KevinQuigs/ECE1896-Force-Feedback-Telepresence-Robot/3D_Printing_Files/Robot/Inmoov Chest - 2175499/files/2pc_Chest__Back__A.stl

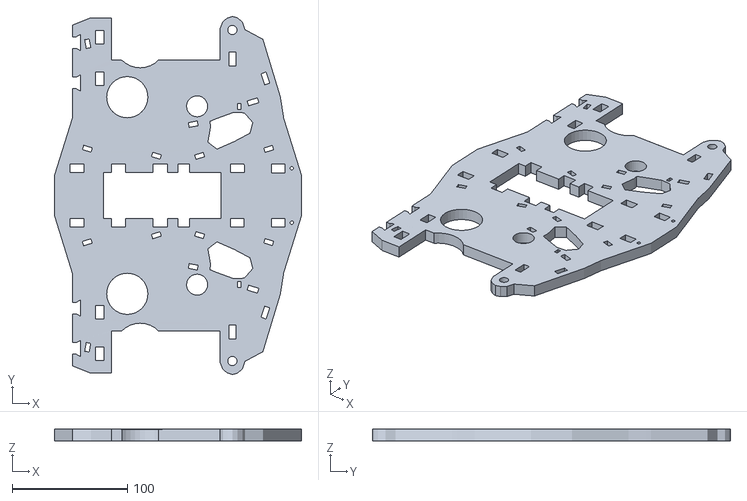
[picture p30: CAD file, 2025-10-10]
3D_Printing_Files/Robot/Inmoov Chest - 2175499/files/2pc_Chest__Back__A.stl
214.0 x 310.3 x 10.0
