KevinQuigs/ECE1896-Force-Feedback-Telepresence-Robot/3D_Printing_Files/Robot/Inmoov-hand-i2/Inmoov-hand-i2/i2_LeftHand/i2_LeftCoverThumbV3.stl

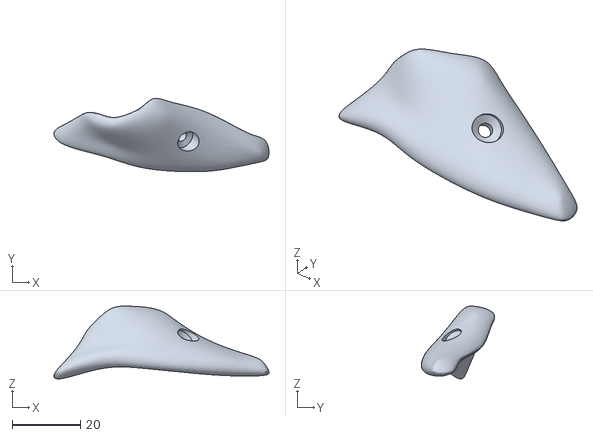
[picture p31: CAD file, 2025-10-01]
3D_Printing_Files/Robot/Inmoov-hand-i2/Inmoov-hand-i2/i2_LeftHand/i2_LeftCoverThumbV3.stl
63.1 x 21.6 x 21.4
