KevinQuigs/ECE1896-Force-Feedback-Telepresence-Robot/3D_Printing_Files/Robot/RoboticHead_Release1/STL/Head_base_mount.stl

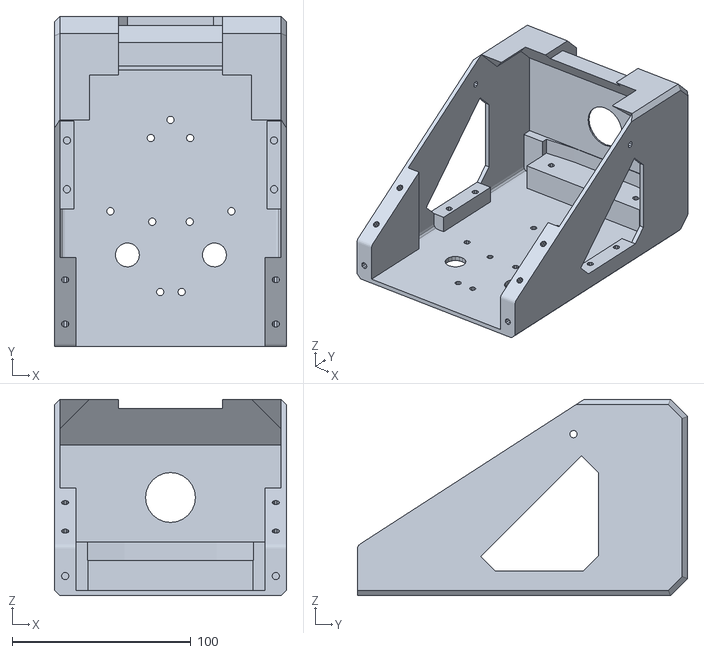
[picture p32: CAD file, 2025-10-10]
3D_Printing_Files/Robot/RoboticHead_Release1/STL/Head_base_mount.stl
130.0 x 184.9 x 110.0
