KevinQuigs/ECE1896-Force-Feedback-Telepresence-Robot/3D_Printing_Files/Robot/RoboticNeck_Release1/STL/Gear_Cover.stl

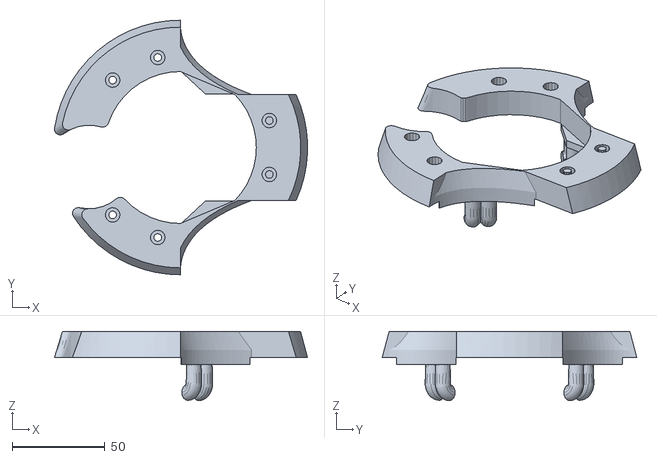
[picture p33: CAD file, 2025-10-10]
3D_Printing_Files/Robot/RoboticNeck_Release1/STL/Gear_Cover.stl
136.3 x 137.2 x 37.4
