KevinQuigs/ECE1896-Force-Feedback-Telepresence-Robot/3D_Printing_Files/Robot/Shoulder for Robot InMoov - 40040/files/servoholderV1.stl

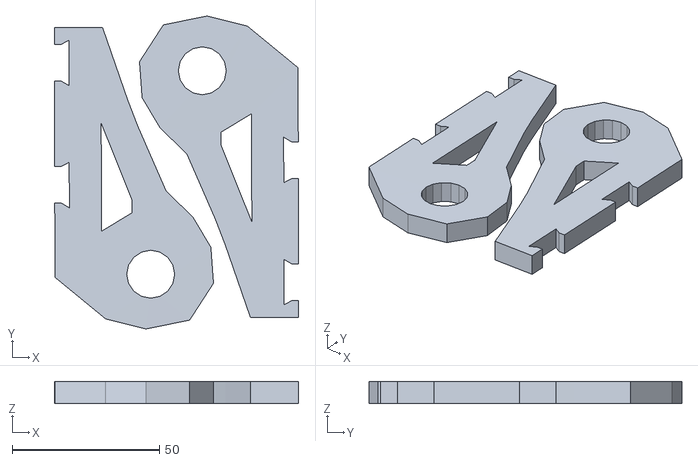
[picture p34: CAD file, 2025-10-01]
3D_Printing_Files/Robot/Shoulder for Robot InMoov - 40040/files/servoholderV1.stl
82.8 x 106.2 x 7.56
