KevinQuigs/ECE1896-Force-Feedback-Telepresence-Robot/3D_Printing_Files/Force_Feedback_Glove/LucidVrGloves/Prot4_EndCap.STL

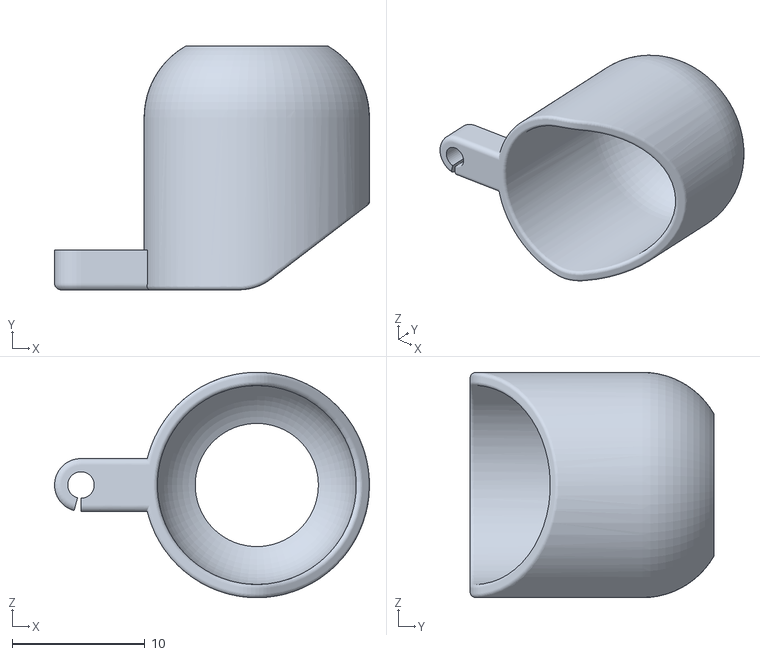
[picture p35: CAD file, 2025-10-01]
3D_Printing_Files/Force_Feedback_Glove/LucidVrGloves/Prot4_EndCap.STL
23.8 x 18.4 x 17.0
