KevinQuigs/ECE1896-Force-Feedback-Telepresence-Robot/3D_Printing_Files/Robot/Inmoov Chest - 2175499/files/4pc_Chest_Front_BottomLeft.stl

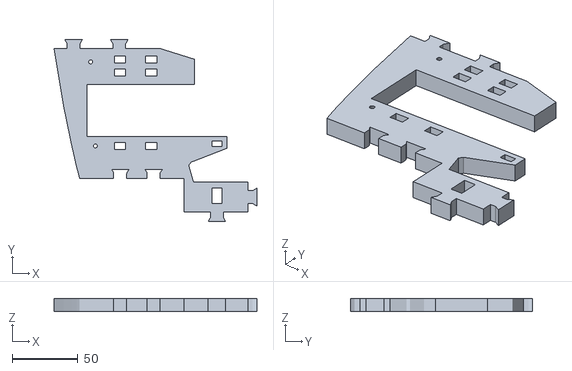
[picture p36: CAD file, 2025-10-10]
3D_Printing_Files/Robot/Inmoov Chest - 2175499/files/4pc_Chest_Front_BottomLeft.stl
154.4 x 138.7 x 10.0
