KevinQuigs/ECE1896-Force-Feedback-Telepresence-Robot/3D_Printing_Files/Robot/Inmoov-hand-i2/Inmoov-hand-i2/i2_RightHand/i2_HandCoverV2.stl

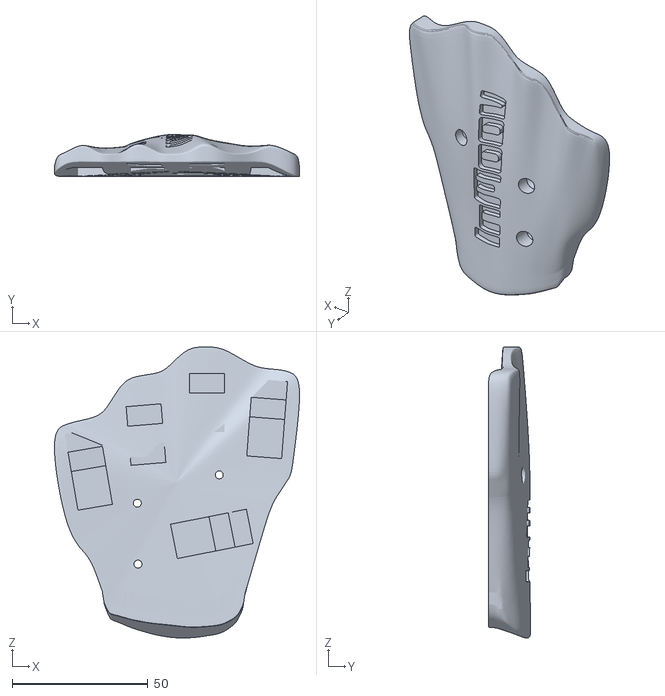
[picture p37: CAD file, 2025-10-01]
3D_Printing_Files/Robot/Inmoov-hand-i2/Inmoov-hand-i2/i2_RightHand/i2_HandCoverV2.stl
90.2 x 15.6 x 107.1
