KevinQuigs/ECE1896-Force-Feedback-Telepresence-Robot/3D_Printing_Files/Robot/RoboticHead_Release1/STL/Head_Handle.stl

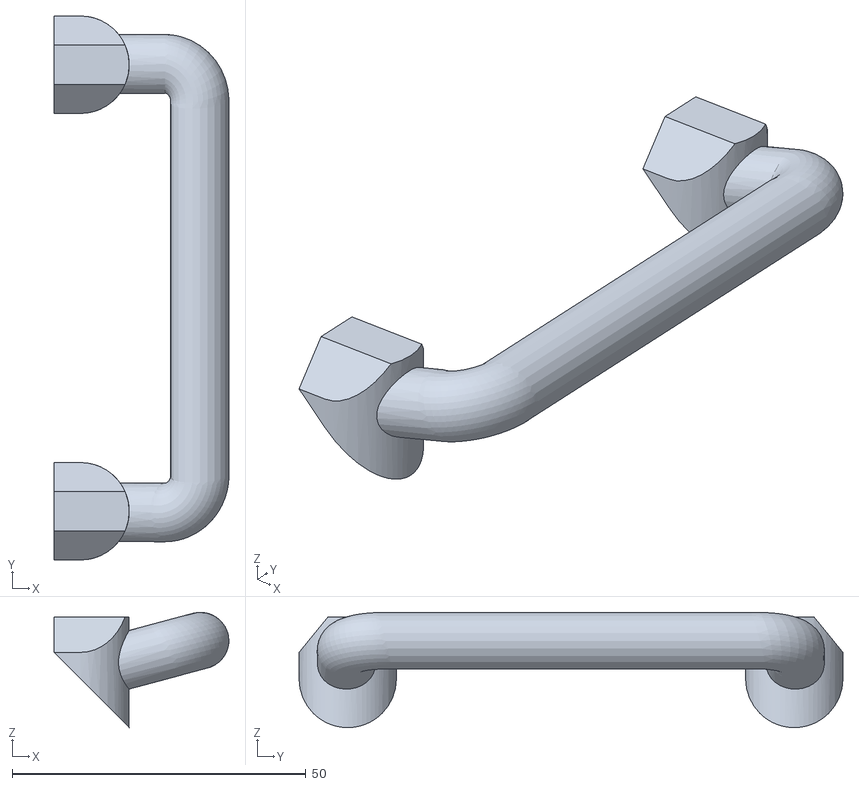
[picture p38: CAD file, 2025-10-10]
3D_Printing_Files/Robot/RoboticHead_Release1/STL/Head_Handle.stl
29.8 x 92.6 x 19.6
