KevinQuigs/ECE1896-Force-Feedback-Telepresence-Robot/3D_Printing_Files/Robot/RoboticNeck_Release1/STL/Test_BearingFilling.stl

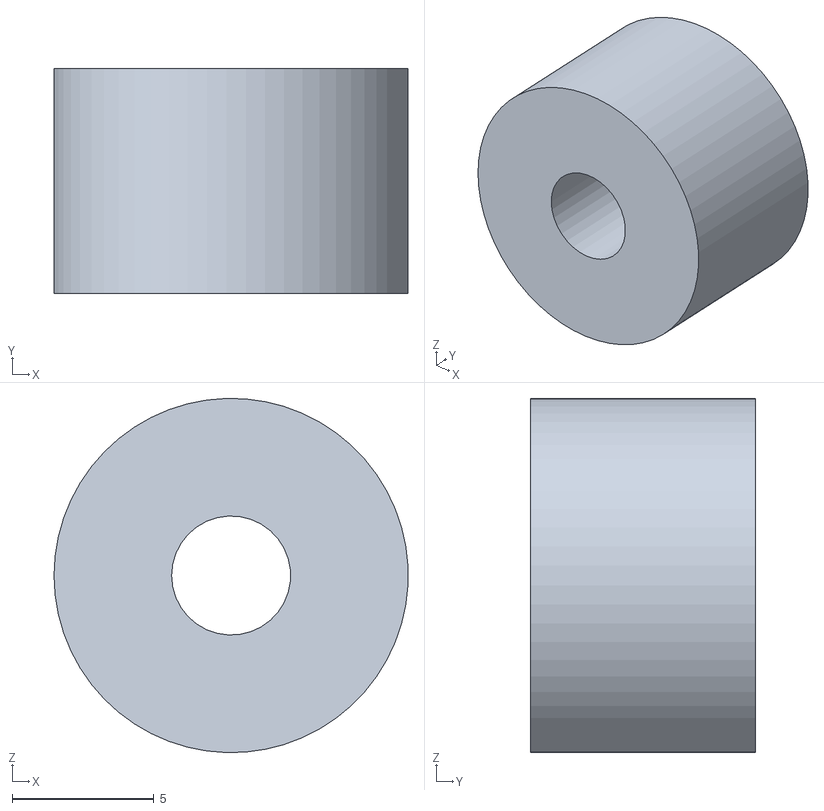
[picture p39: CAD file, 2025-10-10]
3D_Printing_Files/Robot/RoboticNeck_Release1/STL/Test_BearingFilling.stl
12.5 x 7.94 x 12.5
