KevinQuigs/ECE1896-Force-Feedback-Telepresence-Robot/3D_Printing_Files/Robot/Shoulder for Robot InMoov - 40040/files/servoHolsterV1.stl

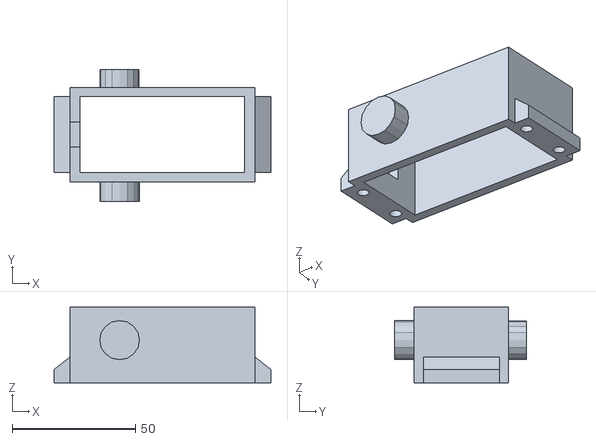
[picture p40: CAD file, 2025-10-01]
3D_Printing_Files/Robot/Shoulder for Robot InMoov - 40040/files/servoHolsterV1.stl
87.9 x 53.5 x 30.7
