KevinQuigs/ECE1896-Force-Feedback-Telepresence-Robot/3D_Printing_Files/Force_Feedback_Glove/LucidVrGloves/GreenPotSildeHolder_Proto4.1.STL

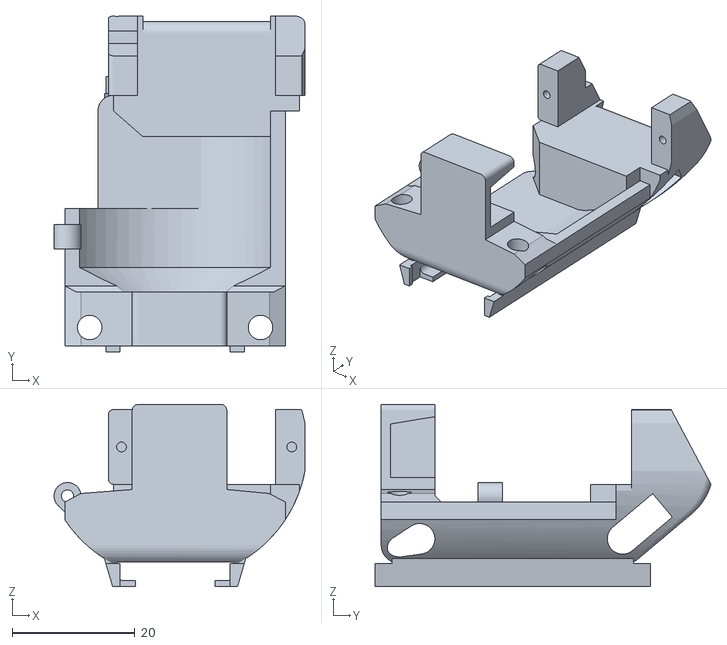
[picture p41: CAD file, 2025-10-01]
3D_Printing_Files/Force_Feedback_Glove/LucidVrGloves/GreenPotSildeHolder_Proto4.1.STL
41.0 x 54.9 x 29.8
