KevinQuigs/ECE1896-Force-Feedback-Telepresence-Robot/3D_Printing_Files/Robot/Inmoov Chest - 2175499/files/8_TEST_JOINT_7_5mm.stl

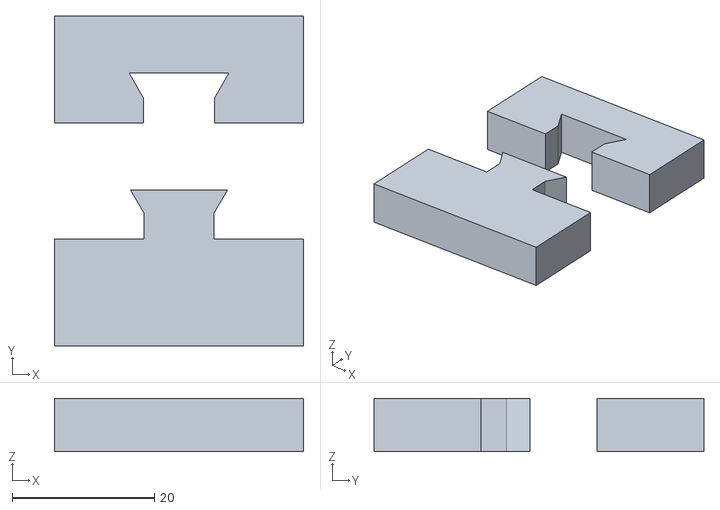
[picture p42: CAD file, 2025-10-10]
3D_Printing_Files/Robot/Inmoov Chest - 2175499/files/8_TEST_JOINT_7_5mm.stl
35.0 x 46.3 x 7.50
