KevinQuigs/ECE1896-Force-Feedback-Telepresence-Robot/3D_Printing_Files/Robot/Inmoov-hand-i2/Inmoov-hand-i2/i2_LeftHand/i2_LeftWristLargeV2.stl

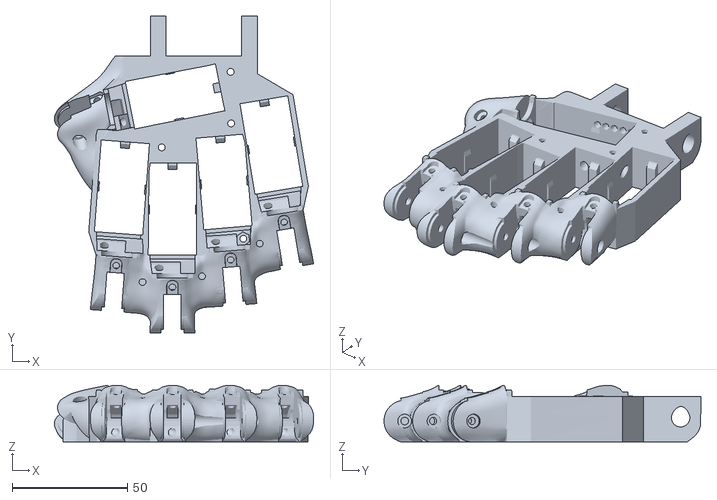
[picture p43: CAD file, 2025-10-01]
3D_Printing_Files/Robot/Inmoov-hand-i2/Inmoov-hand-i2/i2_LeftHand/i2_LeftWristLargeV2.stl
112.6 x 137.7 x 24.5
