KevinQuigs/ECE1896-Force-Feedback-Telepresence-Robot/3D_Printing_Files/Robot/Inmoov-hand-i2/Inmoov-hand-i2/i2_RightHand/i2_FingersTipX5V2.stl

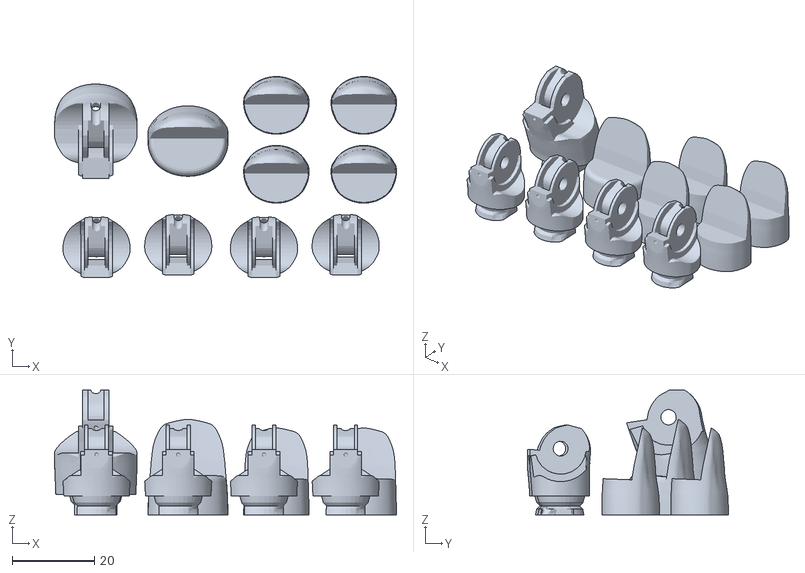
[picture p44: CAD file, 2025-10-01]
3D_Printing_Files/Robot/Inmoov-hand-i2/Inmoov-hand-i2/i2_RightHand/i2_FingersTipX5V2.stl
82.9 x 48.7 x 30.2
