KevinQuigs/ECE1896-Force-Feedback-Telepresence-Robot/3D_Printing_Files/Robot/RoboticHead_Release1/STL/Esp32_Holder.stl

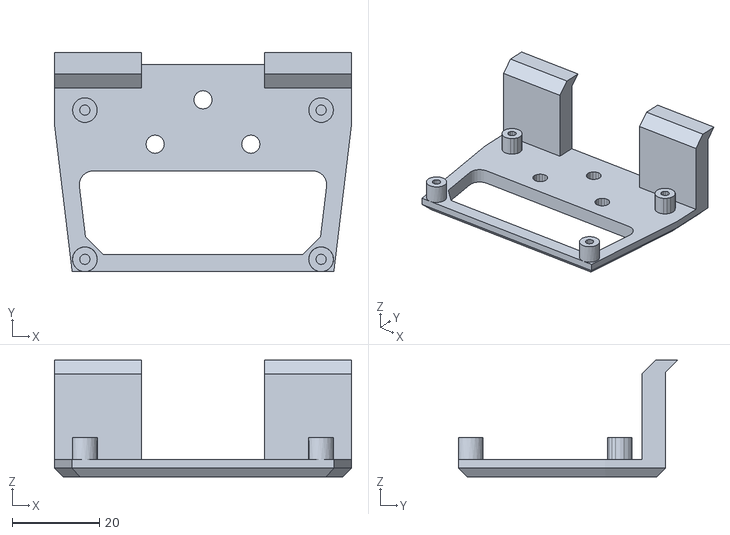
[picture p45: CAD file, 2025-10-10]
3D_Printing_Files/Robot/RoboticHead_Release1/STL/Esp32_Holder.stl
68.3 x 50.4 x 26.8
