KevinQuigs/ECE1896-Force-Feedback-Telepresence-Robot/3D_Printing_Files/Robot/RoboticNeck_Release1/STL/Servo_Pulley.stl

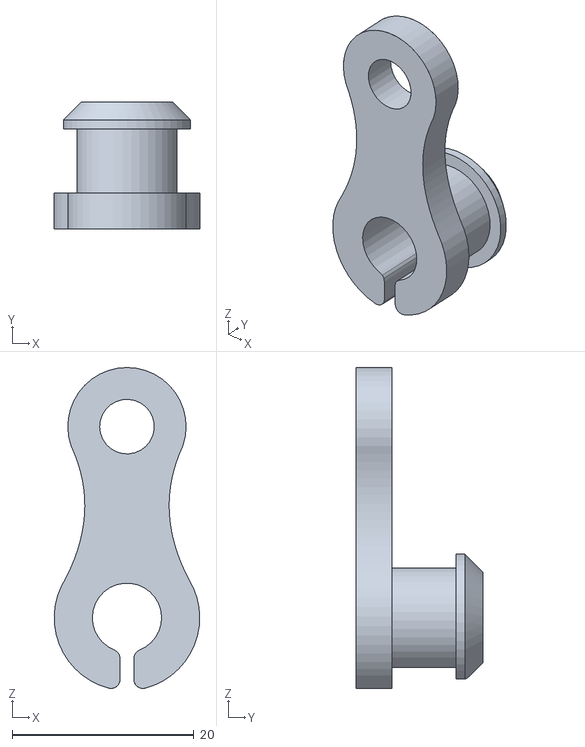
[picture p46: CAD file, 2025-10-10]
3D_Printing_Files/Robot/RoboticNeck_Release1/STL/Servo_Pulley.stl
16.0 x 14.0 x 35.3
