KevinQuigs/ECE1896-Force-Feedback-Telepresence-Robot/3D_Printing_Files/Robot/Shoulder for Robot InMoov - 40040/files/ClaviBackV2.stl

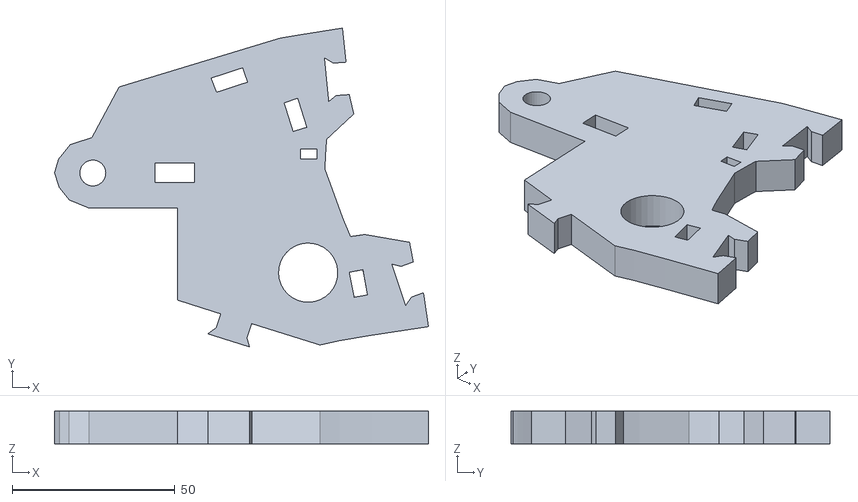
[picture p47: CAD file, 2025-10-01]
3D_Printing_Files/Robot/Shoulder for Robot InMoov - 40040/files/ClaviBackV2.stl
114.9 x 97.9 x 10.0
