KevinQuigs/ECE1896-Force-Feedback-Telepresence-Robot/3D_Printing_Files/Force_Feedback_Glove/LucidVrGloves/Tensioner_GreenPot.STL

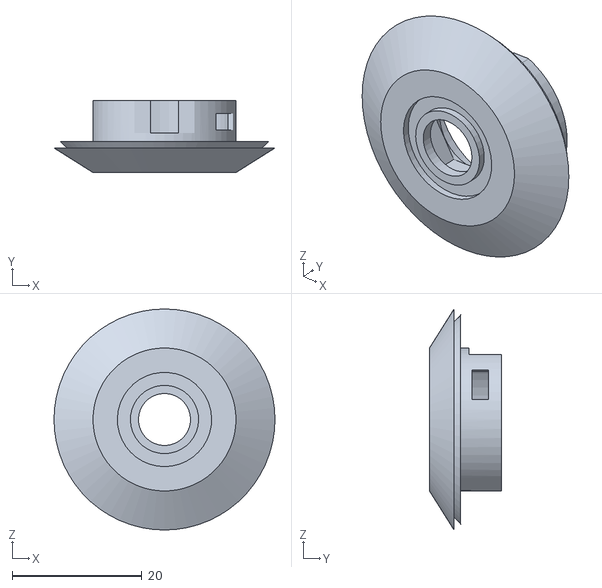
[picture p48: CAD file, 2025-10-01]
3D_Printing_Files/Force_Feedback_Glove/LucidVrGloves/Tensioner_GreenPot.STL
34.0 x 11.1 x 34.0
