KevinQuigs/ECE1896-Force-Feedback-Telepresence-Robot/3D_Printing_Files/Robot/Inmoov Chest - 2175499/files/6_Neck_V3.stl

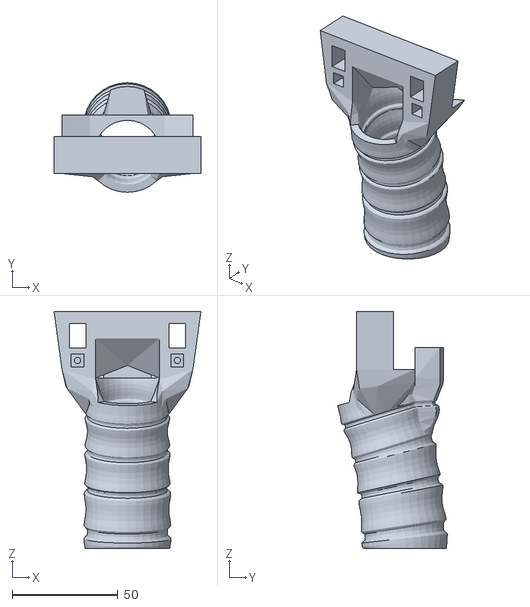
[picture p49: CAD file, 2025-10-10]
3D_Printing_Files/Robot/Inmoov Chest - 2175499/files/6_Neck_V3.stl
69.4 x 51.8 x 112.0
