KevinQuigs/ECE1896-Force-Feedback-Telepresence-Robot/3D_Printing_Files/Robot/Inmoov-hand-i2/Inmoov-hand-i2/i2_RightHand/i2_FingersMoldX5V3.stl

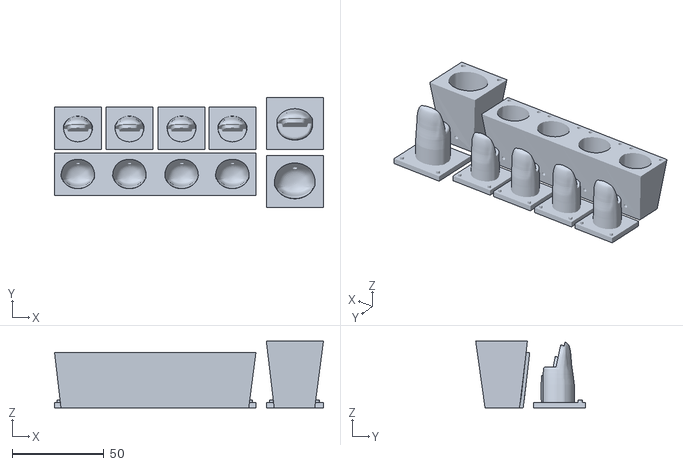
[picture p50: CAD file, 2025-10-01]
3D_Printing_Files/Robot/Inmoov-hand-i2/Inmoov-hand-i2/i2_RightHand/i2_FingersMoldX5V3.stl
146.8 x 59.8 x 36.5
