KevinQuigs/ECE1896-Force-Feedback-Telepresence-Robot/3D_Printing_Files/Robot/RoboticHead_Release1/STL/RaspberryPi_IO_Shield.stl

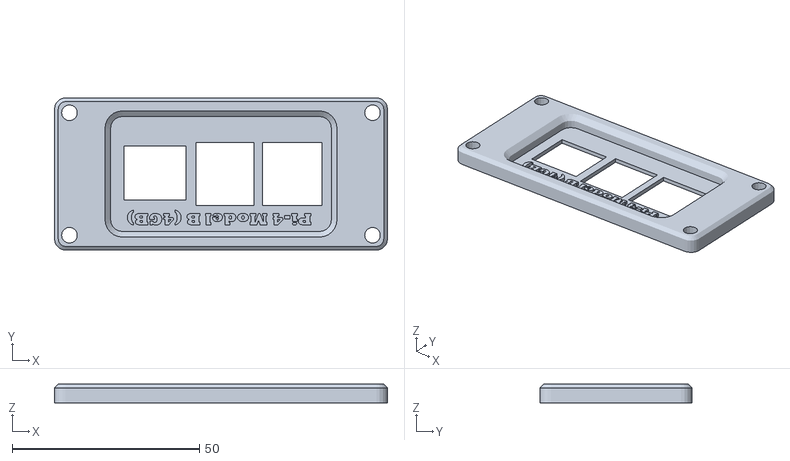
[picture p51: CAD file, 2025-10-10]
3D_Printing_Files/Robot/RoboticHead_Release1/STL/RaspberryPi_IO_Shield.stl
89.0 x 40.7 x 5.00
