KevinQuigs/ECE1896-Force-Feedback-Telepresence-Robot/3D_Printing_Files/Robot/RoboticNeck_Release1/STL/Gear_Baseplate_2.stl

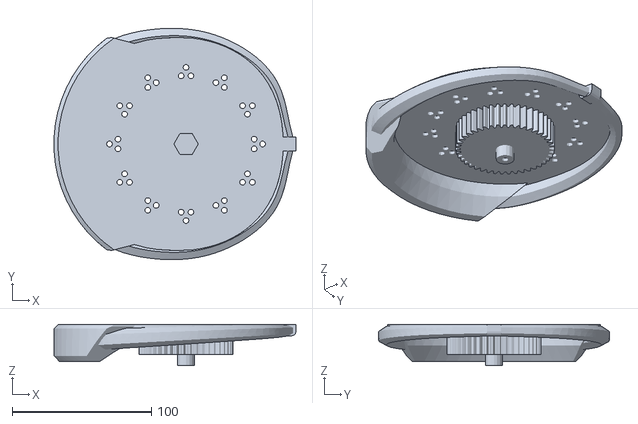
[picture p52: CAD file, 2025-10-10]
3D_Printing_Files/Robot/RoboticNeck_Release1/STL/Gear_Baseplate_2.stl
173.9 x 166.3 x 29.5
