KevinQuigs/ECE1896-Force-Feedback-Telepresence-Robot/3D_Printing_Files/Robot/Shoulder for Robot InMoov - 40040/files/LeftPivPotholderV2.stl

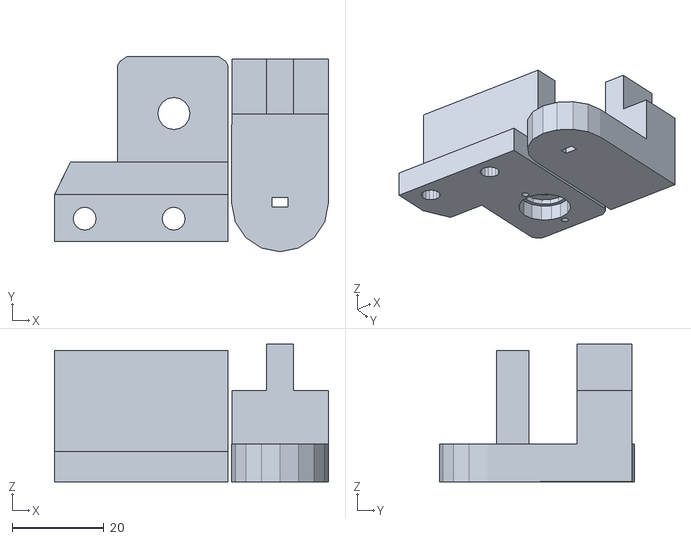
[picture p53: CAD file, 2025-10-01]
3D_Printing_Files/Robot/Shoulder for Robot InMoov - 40040/files/LeftPivPotholderV2.stl
59.6 x 42.5 x 30.0
