KevinQuigs/ECE1896-Force-Feedback-Telepresence-Robot/3D_Printing_Files/Force_Feedback_Glove/LucidVrGloves/RigidMount_leftHand.STL

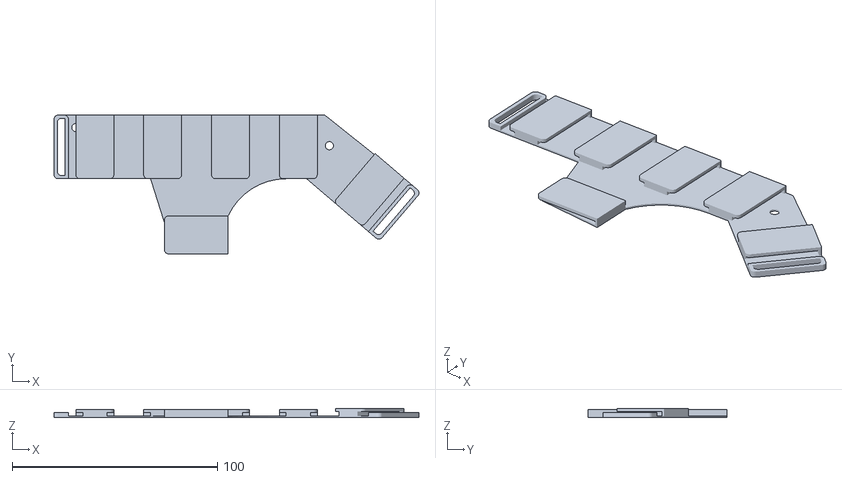
[picture p54: CAD file, 2025-10-01]
3D_Printing_Files/Force_Feedback_Glove/LucidVrGloves/RigidMount_leftHand.STL
177.7 x 67.6 x 4.60
