KevinQuigs/ECE1896-Force-Feedback-Telepresence-Robot/3D_Printing_Files/Robot/Inmoov Chest - 2175499/files/1pc_Chest__Front.stl

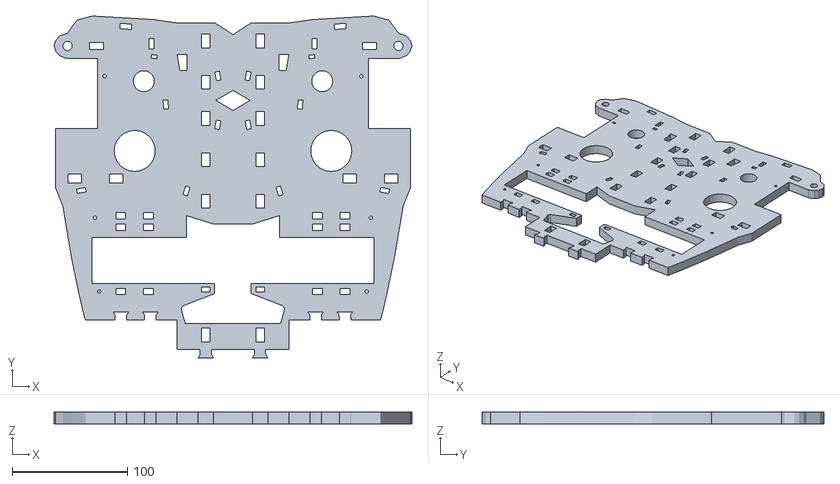
[picture p55: CAD file, 2025-10-10]
3D_Printing_Files/Robot/Inmoov Chest - 2175499/files/1pc_Chest__Front.stl
310.3 x 296.4 x 10.0
