KevinQuigs/ECE1896-Force-Feedback-Telepresence-Robot/3D_Printing_Files/Robot/Inmoov-hand-i2/Inmoov-hand-i2/i2_LeftHand/i2_Adapter1109MG.stl

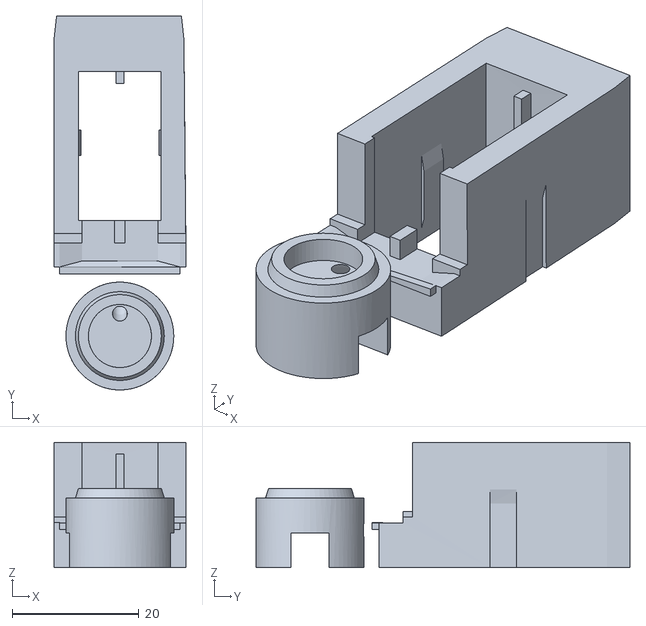
[picture p56: CAD file, 2025-10-01]
3D_Printing_Files/Robot/Inmoov-hand-i2/Inmoov-hand-i2/i2_LeftHand/i2_Adapter1109MG.stl
20.8 x 58.9 x 19.8
