KevinQuigs/ECE1896-Force-Feedback-Telepresence-Robot/3D_Printing_Files/Robot/Inmoov-hand-i2/Inmoov-hand-i2/i2_RightHand/i2_CoverFingerV3.stl

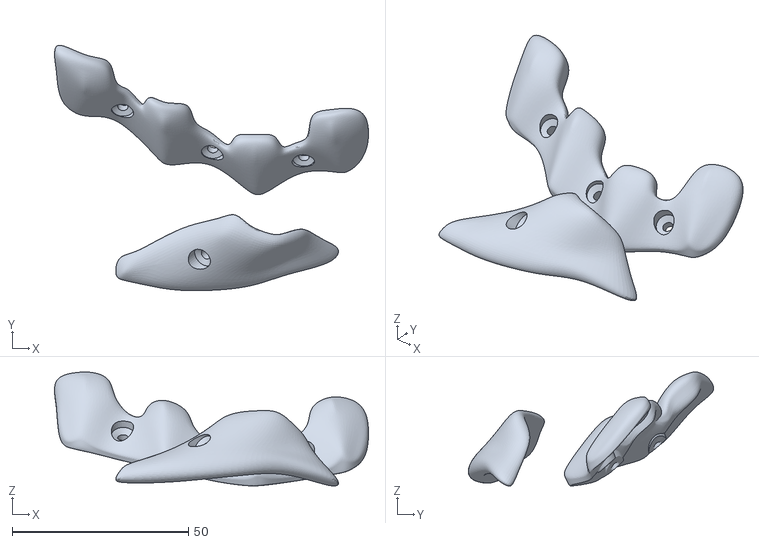
[picture p57: CAD file, 2025-10-01]
3D_Printing_Files/Robot/Inmoov-hand-i2/Inmoov-hand-i2/i2_RightHand/i2_CoverFingerV3.stl
89.0 x 69.6 x 32.3
