KevinQuigs/ECE1896-Force-Feedback-Telepresence-Robot/3D_Printing_Files/Robot/RoboticHead_Release1/STL/Head_Top.stl

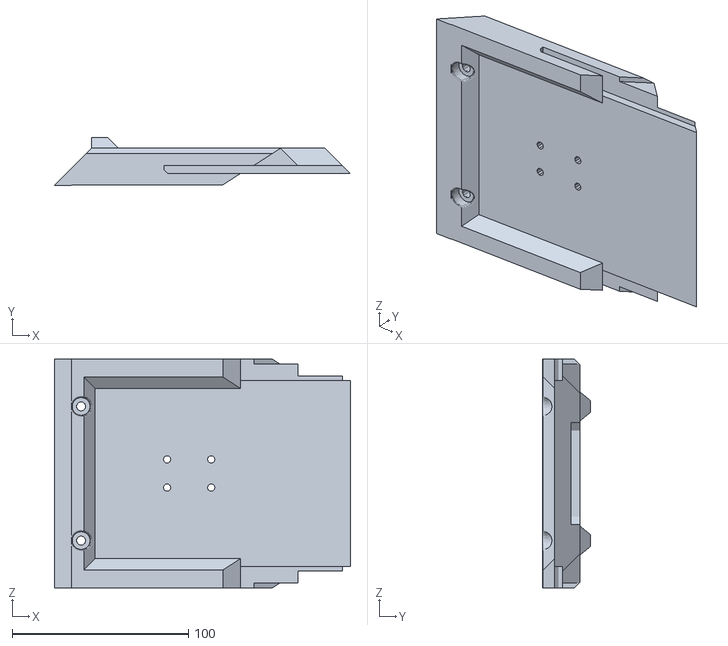
[picture p58: CAD file, 2025-10-10]
3D_Printing_Files/Robot/RoboticHead_Release1/STL/Head_Top.stl
167.7 x 27.1 x 129.6
