KevinQuigs/ECE1896-Force-Feedback-Telepresence-Robot/3D_Printing_Files/Robot/RoboticNeck_Release1/STL/Neck_Cover.stl

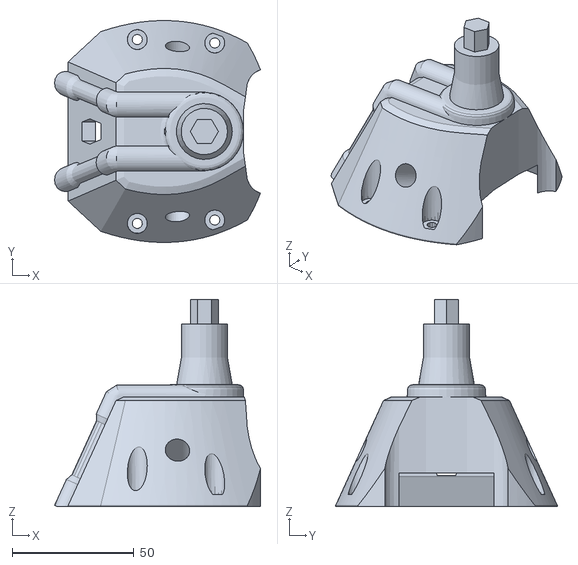
[picture p59: CAD file, 2025-10-10]
3D_Printing_Files/Robot/RoboticNeck_Release1/STL/Neck_Cover.stl
84.5 x 91.0 x 85.0
