KevinQuigs/ECE1896-Force-Feedback-Telepresence-Robot/3D_Printing_Files/Robot/Shoulder for Robot InMoov - 40040/files/PivWormV2.stl

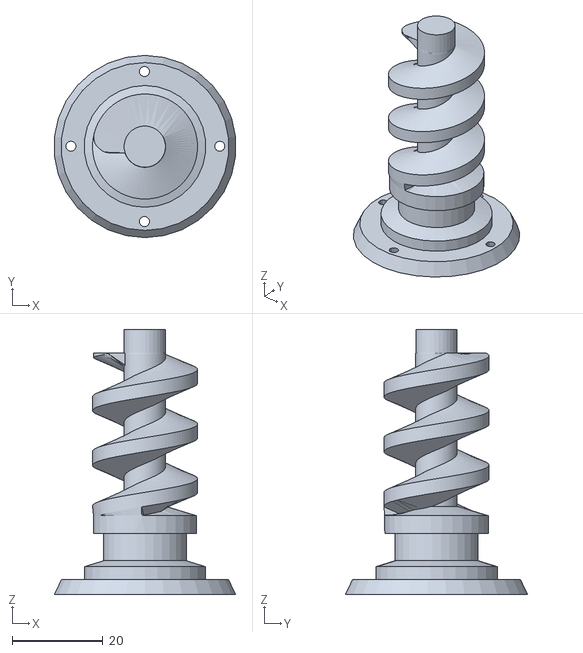
[picture p60: CAD file, 2025-10-01]
3D_Printing_Files/Robot/Shoulder for Robot InMoov - 40040/files/PivWormV2.stl
39.9 x 40.2 x 58.4
