KevinQuigs/ECE1896-Force-Feedback-Telepresence-Robot/3D_Printing_Files/Robot/Inmoov-hand-i2/Inmoov-hand-i2/i2_LeftHand/i2_LeftWristGearV1.stl

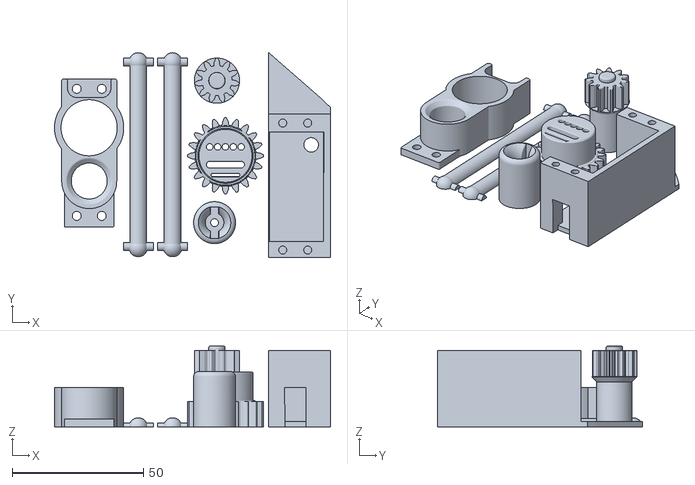
[picture p62: CAD file, 2025-10-01]
3D_Printing_Files/Robot/Inmoov-hand-i2/Inmoov-hand-i2/i2_LeftHand/i2_LeftWristGearV1.stl
105.2 x 78.1 x 30.8
