KevinQuigs/ECE1896-Force-Feedback-Telepresence-Robot/3D_Printing_Files/Robot/Inmoov-hand-i2/Inmoov-hand-i2/i2_RightHand/i2_PulleyX5V1.stl

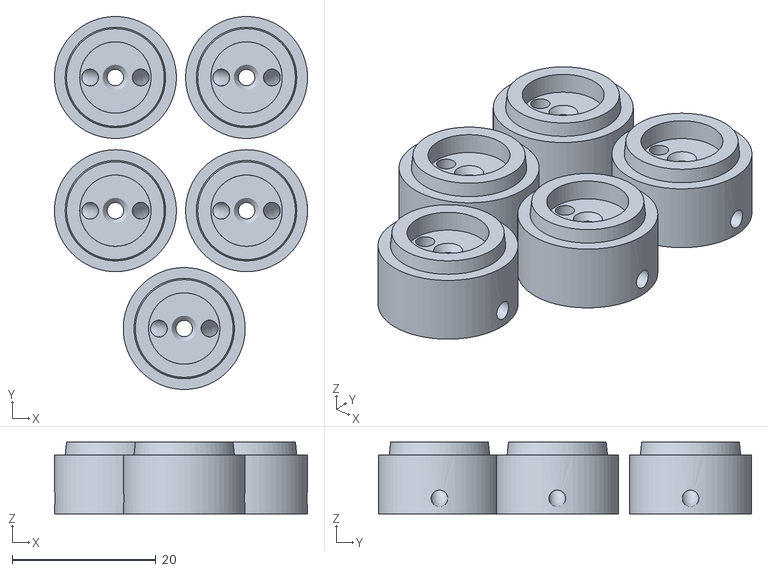
[picture p63: CAD file, 2025-10-01]
3D_Printing_Files/Robot/Inmoov-hand-i2/Inmoov-hand-i2/i2_RightHand/i2_PulleyX5V1.stl
35.3 x 52.0 x 10.0
