KevinQuigs/ECE1896-Force-Feedback-Telepresence-Robot/3D_Printing_Files/Robot/RoboticHead_Release1/STL/Neck_Baseplate_V2.stl

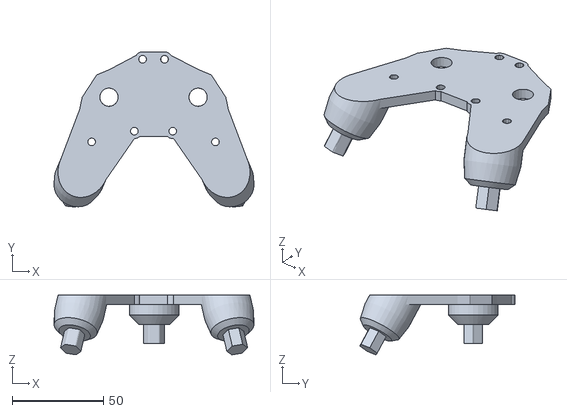
[picture p64: CAD file, 2025-10-10]
3D_Printing_Files/Robot/RoboticHead_Release1/STL/Neck_Baseplate_V2.stl
109.5 x 85.1 x 32.7
