KevinQuigs/ECE1896-Force-Feedback-Telepresence-Robot/3D_Printing_Files/Robot/Inmoov Chest - 2175499/files/7_Neck_Joiner_Mount.stl

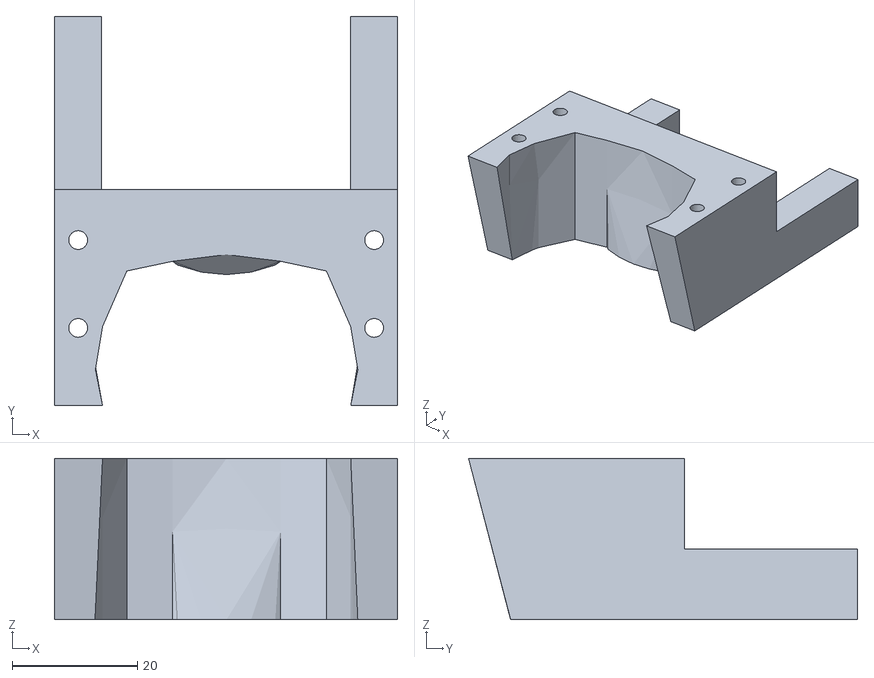
[picture p67: CAD file, 2025-10-10]
3D_Printing_Files/Robot/Inmoov Chest - 2175499/files/7_Neck_Joiner_Mount.stl
54.7 x 62.0 x 25.7
