KevinQuigs/ECE1896-Force-Feedback-Telepresence-Robot/3D_Printing_Files/Robot/RoboticHead_Release1/STL/Camera_Clip.stl

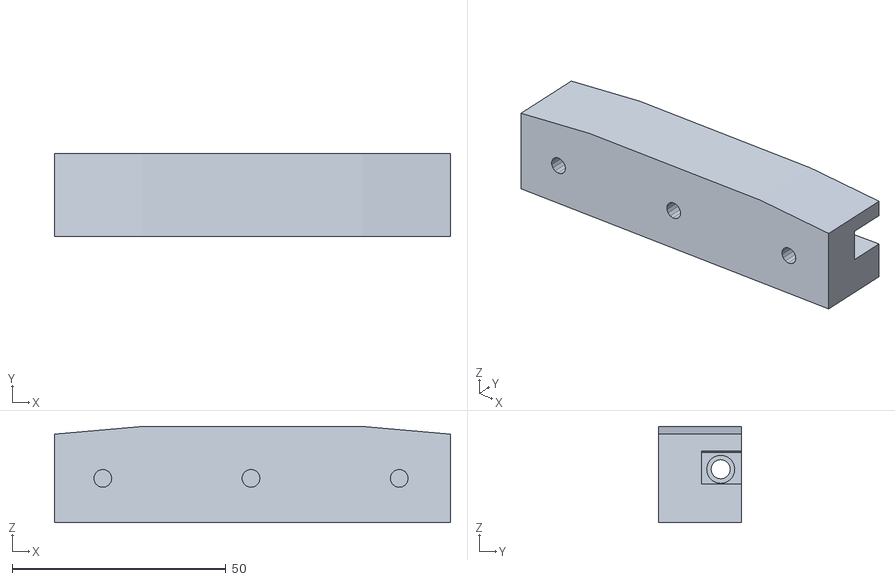
[picture p68: CAD file, 2025-10-10]
3D_Printing_Files/Robot/RoboticHead_Release1/STL/Camera_Clip.stl
92.7 x 19.4 x 22.5
