KevinQuigs/ECE1896-Force-Feedback-Telepresence-Robot/3D_Printing_Files/Robot/RoboticNeck_Release1/STL/Servo_Shaft_2.stl

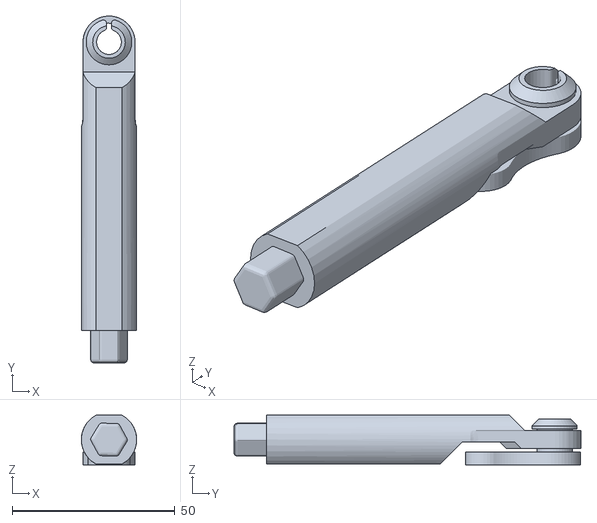
[picture p69: CAD file, 2025-10-10]
3D_Printing_Files/Robot/RoboticNeck_Release1/STL/Servo_Shaft_2.stl
17.0 x 106.5 x 15.3
