KevinQuigs/ECE1896-Force-Feedback-Telepresence-Robot/3D_Printing_Files/Robot/Inmoov Chest - 2175499/files/4pc_Chest_Back_TopLeft.stl

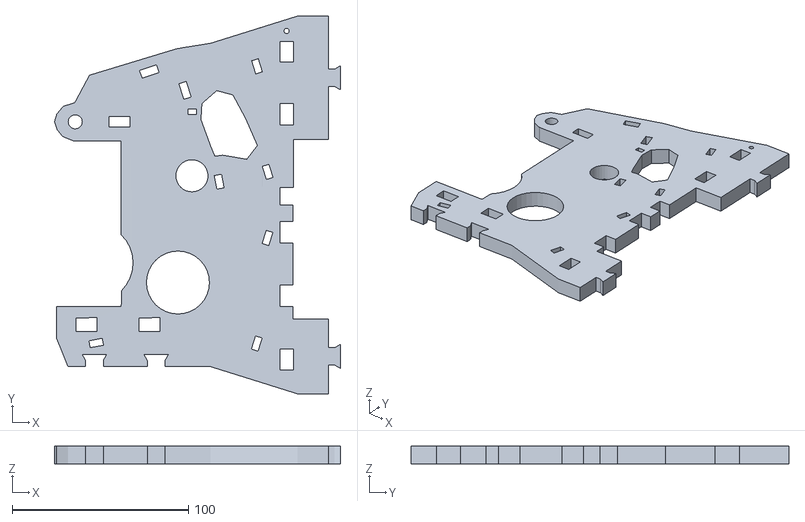
[picture p71: CAD file, 2025-10-10]
3D_Printing_Files/Robot/Inmoov Chest - 2175499/files/4pc_Chest_Back_TopLeft.stl
162.1 x 214.0 x 10.0
