KevinQuigs/ECE1896-Force-Feedback-Telepresence-Robot/3D_Printing_Files/Robot/RoboticHead_Release1/STL/Head_Fin.stl

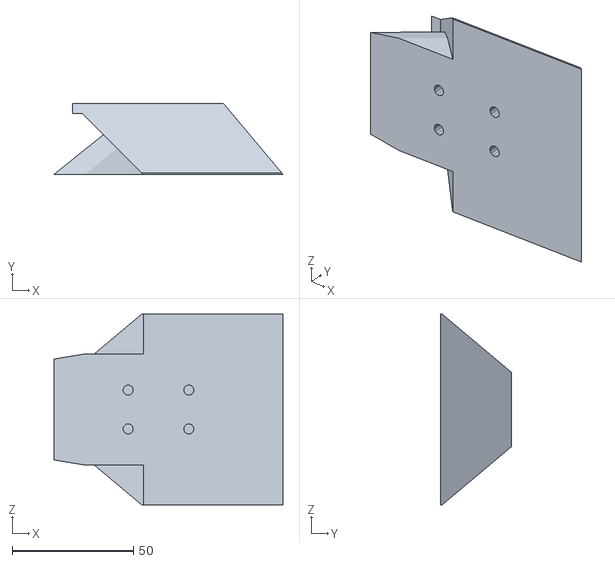
[picture p72: CAD file, 2025-10-10]
3D_Printing_Files/Robot/RoboticHead_Release1/STL/Head_Fin.stl
94.4 x 29.2 x 78.7
