KevinQuigs/ECE1896-Force-Feedback-Telepresence-Robot/3D_Printing_Files/Robot/RoboticHead_Release1/STL/Neck_Cover_United.stl

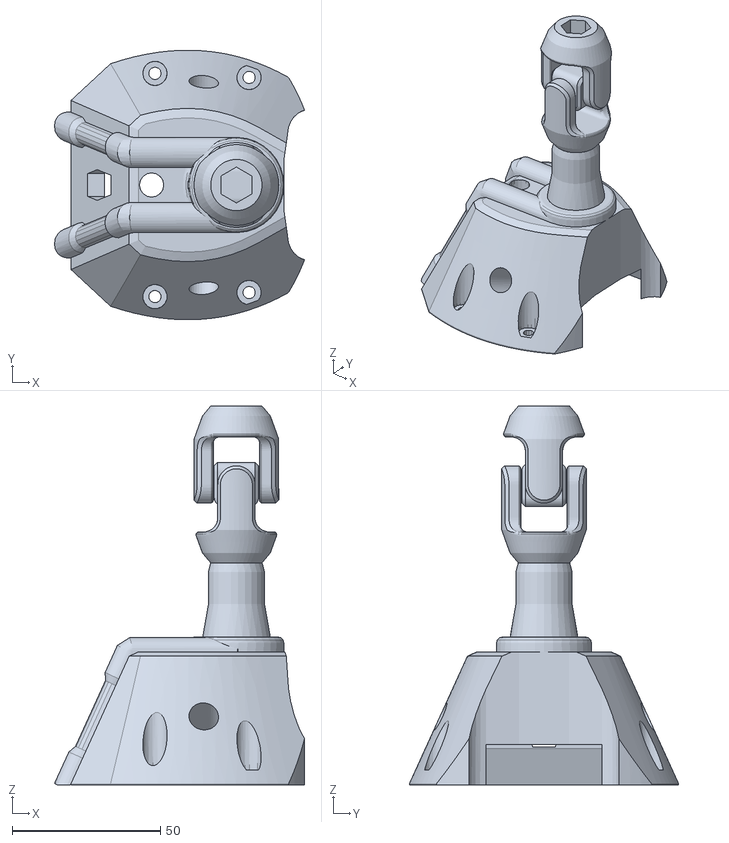
[picture p75: CAD file, 2025-10-10]
3D_Printing_Files/Robot/RoboticHead_Release1/STL/Neck_Cover_United.stl
84.5 x 91.0 x 128.0
