KevinQuigs/ECE1896-Force-Feedback-Telepresence-Robot/3D_Printing_Files/Robot/RoboticNeck_Release1/STL/Head_CameraPanel_Bottom.stl

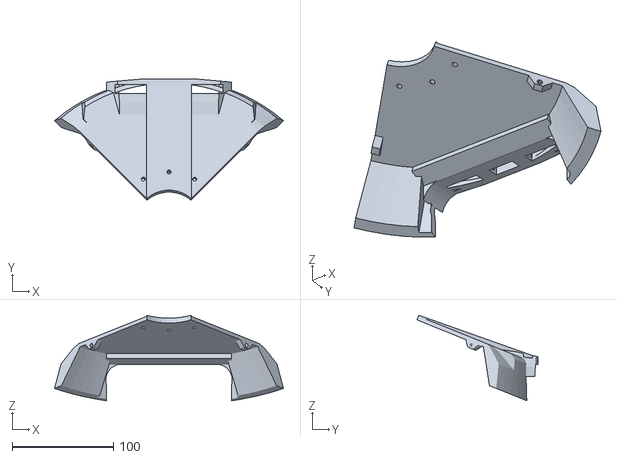
[picture p76: CAD file, 2025-10-10]
3D_Printing_Files/Robot/RoboticNeck_Release1/STL/Head_CameraPanel_Bottom.stl
226.3 x 119.8 x 84.6
