KevinQuigs/ECE1896-Force-Feedback-Telepresence-Robot/3D_Printing_Files/Robot/RoboticHead_Release1/STL/Head_Left_Panel.stl

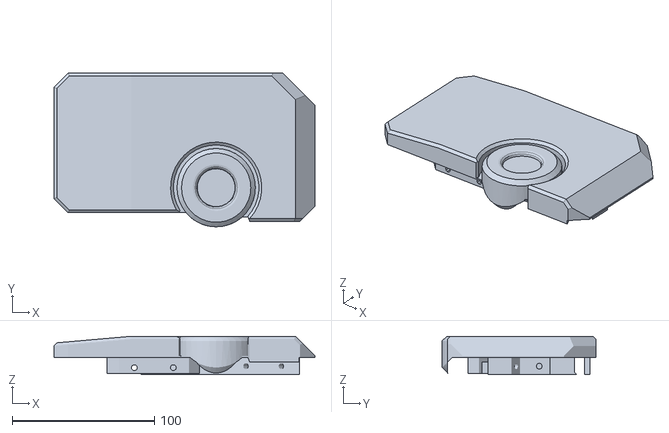
[picture p79: CAD file, 2025-10-10]
3D_Printing_Files/Robot/RoboticHead_Release1/STL/Head_Left_Panel.stl
183.2 x 107.9 x 27.0
