KevinQuigs/ECE1896-Force-Feedback-Telepresence-Robot/3D_Printing_Files/Robot/Inmoov Chest - 2175499/files/4pc_Chest_Back_TopRight.stl

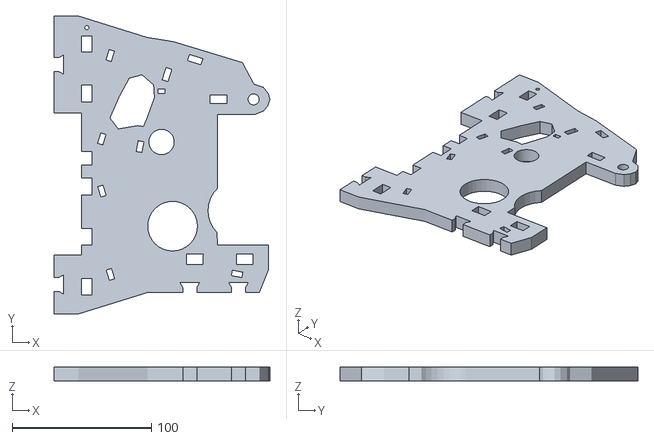
[picture p81: CAD file, 2025-10-10]
3D_Printing_Files/Robot/Inmoov Chest - 2175499/files/4pc_Chest_Back_TopRight.stl
155.2 x 214.0 x 10.0
