KevinQuigs/ECE1896-Force-Feedback-Telepresence-Robot/3D_Printing_Files/Robot/Inmoov Chest - 2175499/files/2pc_Chest_Front_B.stl

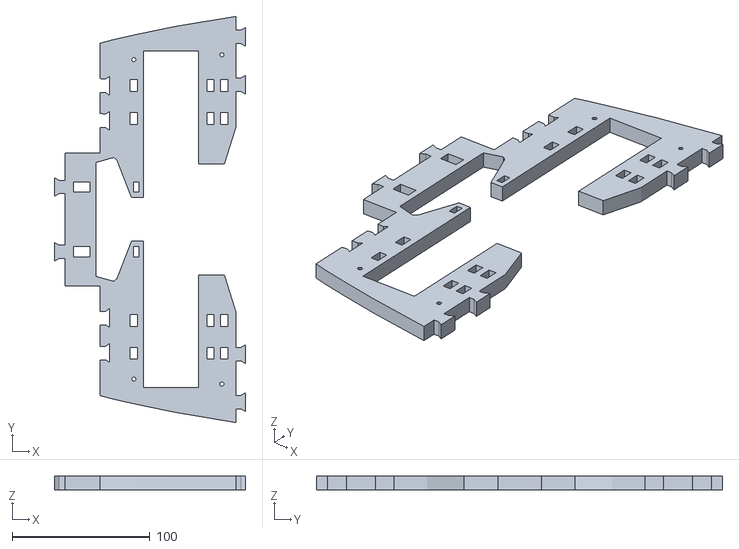
[picture p83: CAD file, 2025-10-10]
3D_Printing_Files/Robot/Inmoov Chest - 2175499/files/2pc_Chest_Front_B.stl
138.7 x 295.0 x 10.0
