KevinQuigs/ECE1896-Force-Feedback-Telepresence-Robot/3D_Printing_Files/Robot/RoboticNeck_Release1/STL/Universal_Joint_Connector.stl

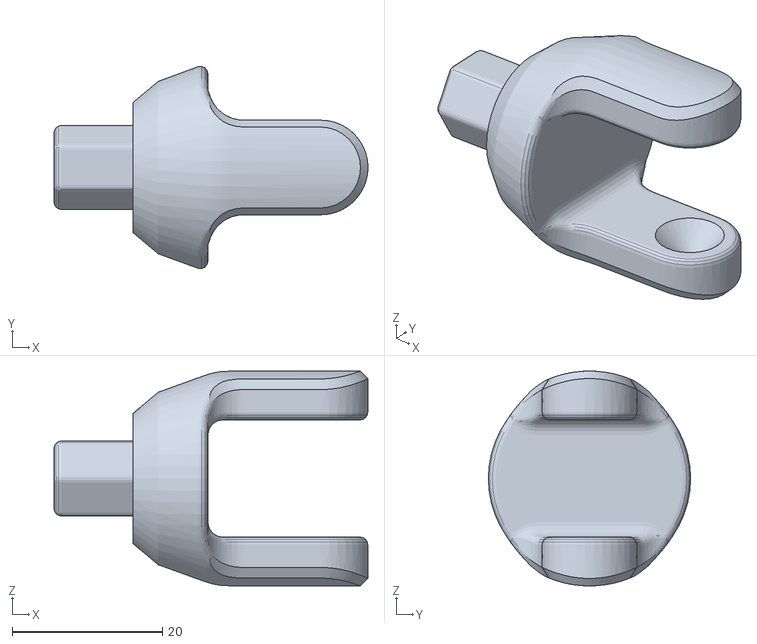
[picture p85: CAD file, 2025-10-10]
3D_Printing_Files/Robot/RoboticNeck_Release1/STL/Universal_Joint_Connector.stl
41.8 x 26.9 x 28.6
