KevinQuigs/ECE1896-Force-Feedback-Telepresence-Robot/3D_Printing_Files/Robot/Inmoov Chest - 2175499/files/4pc_Chest_Back_BottomRight.stl

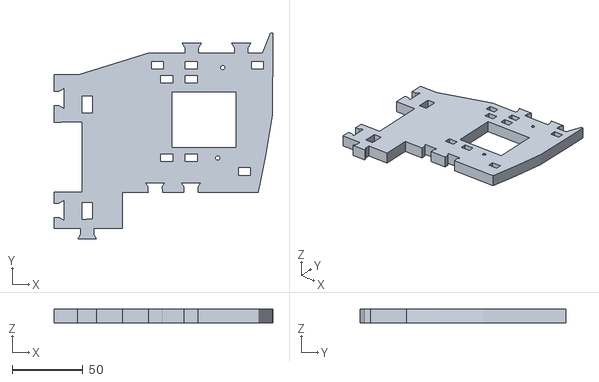
[picture p87: CAD file, 2025-10-10]
3D_Printing_Files/Robot/Inmoov Chest - 2175499/files/4pc_Chest_Back_BottomRight.stl
155.1 x 146.1 x 10.0
