KevinQuigs/ECE1896-Force-Feedback-Telepresence-Robot/3D_Printing_Files/Robot/Inmoov Chest - 2175499/files/2pc_Chest__Back_B.stl

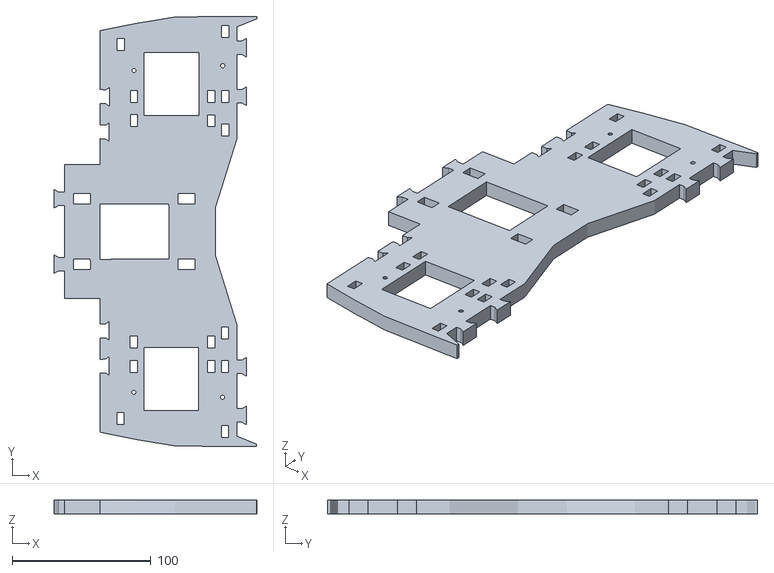
[picture p89: CAD file, 2025-10-10]
3D_Printing_Files/Robot/Inmoov Chest - 2175499/files/2pc_Chest__Back_B.stl
146.3 x 310.1 x 10.0
