KevinQuigs/ECE1896-Force-Feedback-Telepresence-Robot/3D_Printing_Files/Robot/Inmoov Chest - 2175499/files/8_TEST_JOINT_10mm.stl

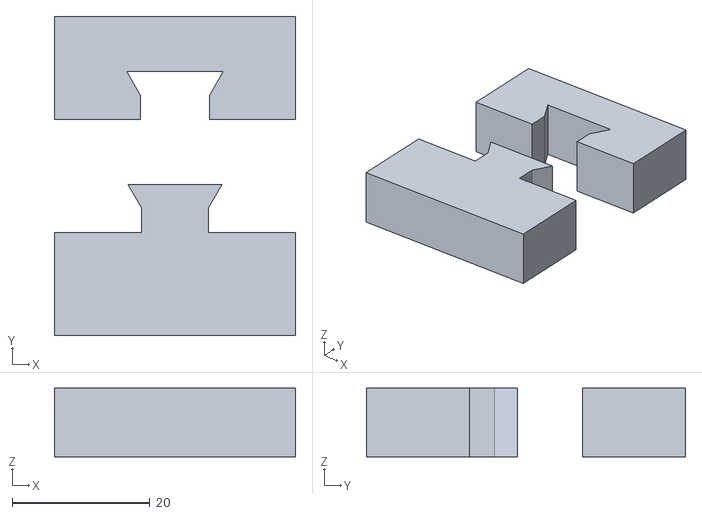
[picture p93: CAD file, 2025-10-10]
3D_Printing_Files/Robot/Inmoov Chest - 2175499/files/8_TEST_JOINT_10mm.stl
35.0 x 46.3 x 10.0
