KevinQuigs/ECE1896-Force-Feedback-Telepresence-Robot/3D_Printing_Files/Robot/RoboticNeck_Release1/STL/Head_Baseplate_extended.stl

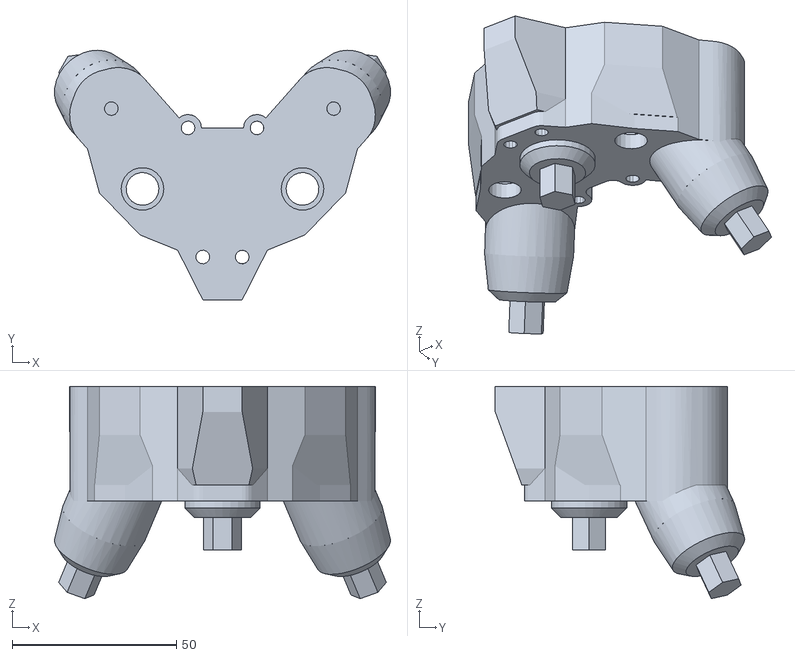
[picture p94: CAD file, 2025-10-10]
3D_Printing_Files/Robot/RoboticNeck_Release1/STL/Head_Baseplate_extended.stl
102.4 x 76.1 x 64.7
