KevinQuigs/ECE1896-Force-Feedback-Telepresence-Robot/3D_Printing_Files/Force_Feedback_Glove/LucidVrGloves/Lucid_VR_simplified.jpg

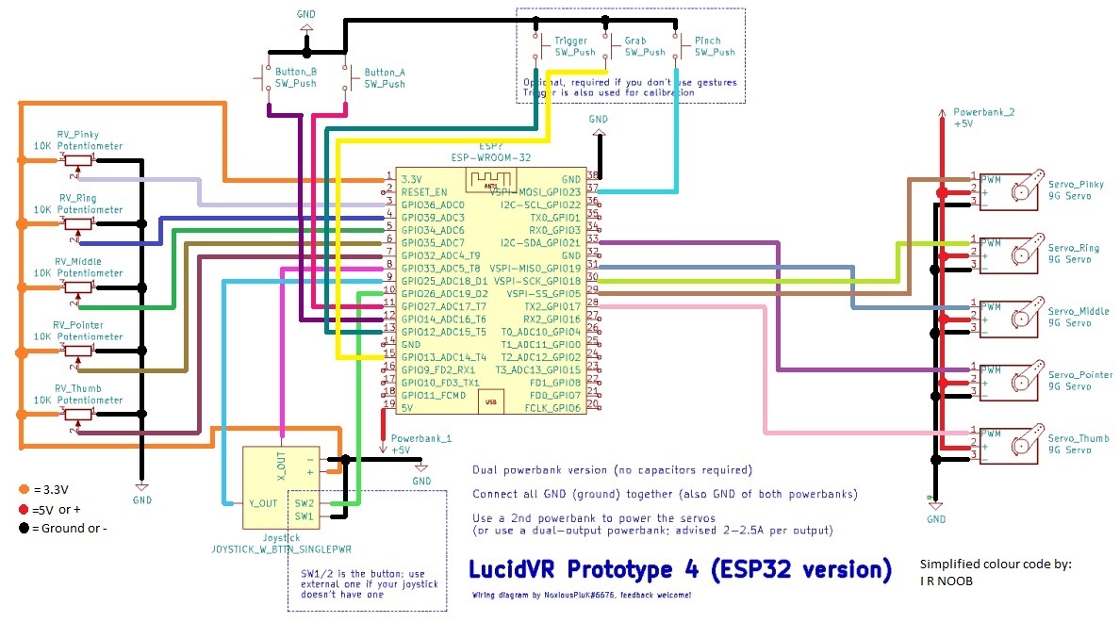
3D_Printing_Files/Force_Feedback_Glove/LucidVrGloves/Lucid_VR_simplified.jpg
