KevinQuigs/ECE1896-Force-Feedback-Telepresence-Robot/3D_Printing_Files/Robot/Inmoov Chest - 2175499/images/3f94c0d6889f5eb2ad75c2c9b5a4ea1a.png

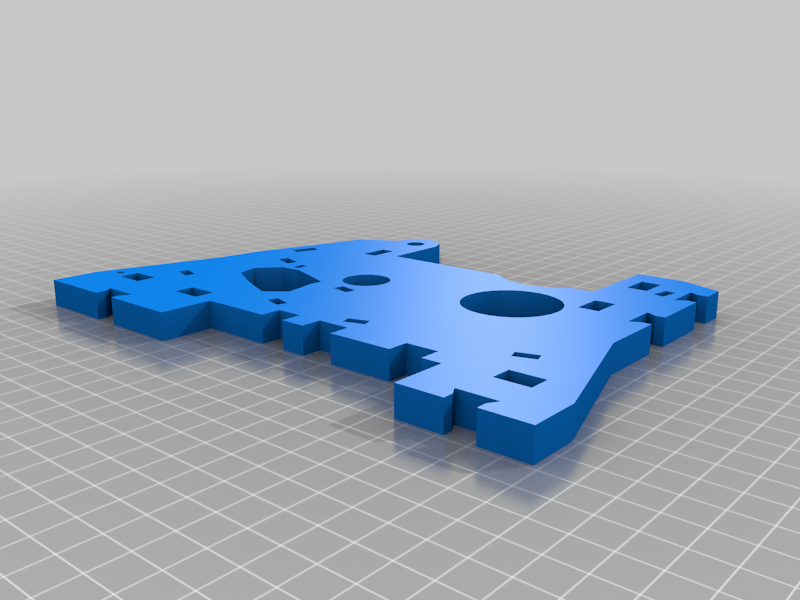
3D_Printing_Files/Robot/Inmoov Chest - 2175499/images/3f94c0d6889f5eb2ad75c2c9b5a4ea1a.png
