KevinQuigs/ECE1896-Force-Feedback-Telepresence-Robot/3D_Printing_Files/Robot/Inmoov Chest - 2175499/images/5ebb07adde3e970d01e14a7a2c740985.png

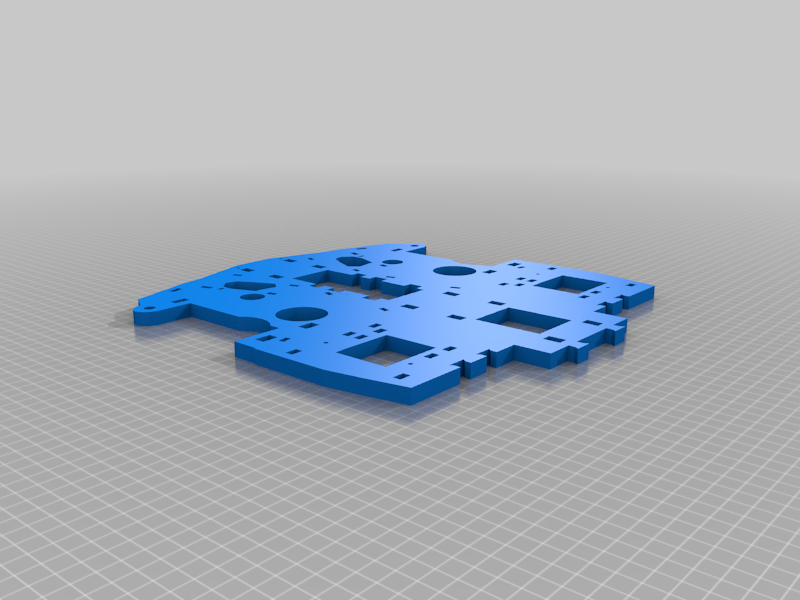
3D_Printing_Files/Robot/Inmoov Chest - 2175499/images/5ebb07adde3e970d01e14a7a2c740985.png
