KevinQuigs/ECE1896-Force-Feedback-Telepresence-Robot/3D_Printing_Files/Robot/Inmoov Chest - 2175499/images/94c31a3c0123b195206af8c7d3642fea.png

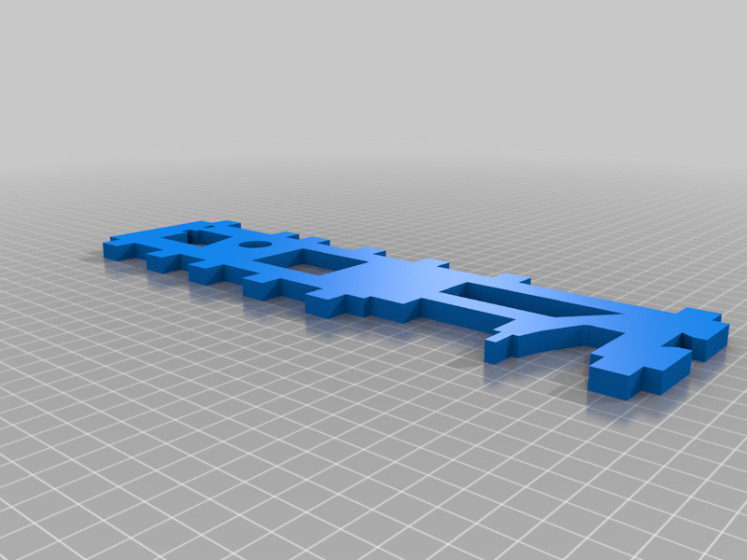
3D_Printing_Files/Robot/Inmoov Chest - 2175499/images/94c31a3c0123b195206af8c7d3642fea.png
