KevinQuigs/ECE1896-Force-Feedback-Telepresence-Robot/3D_Printing_Files/Robot/Inmoov Chest - 2175499/images/97d2c1d26a01719e6a1cca5ebc9adbdb.png

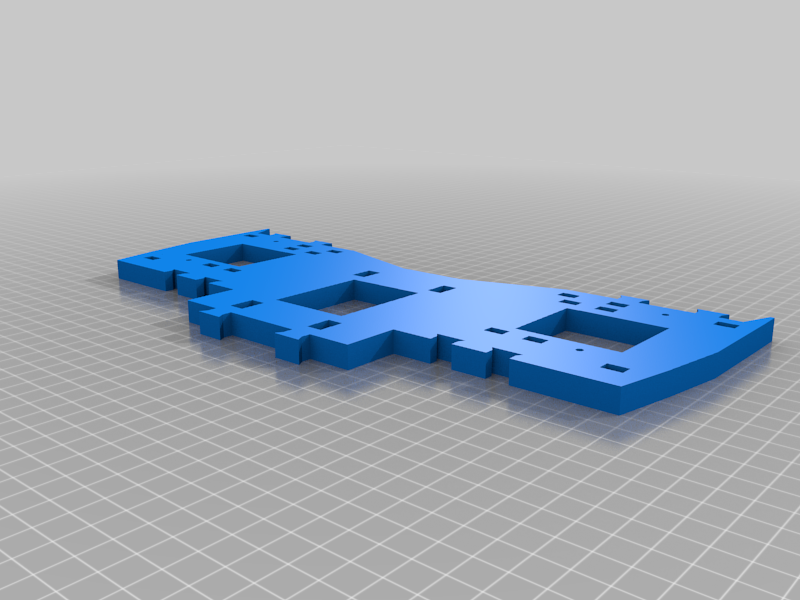
3D_Printing_Files/Robot/Inmoov Chest - 2175499/images/97d2c1d26a01719e6a1cca5ebc9adbdb.png
