KevinQuigs/ECE1896-Force-Feedback-Telepresence-Robot/3D_Printing_Files/Robot/Inmoov Chest - 2175499/images/3088fcb493d6a2ad61c758510ab16376.png

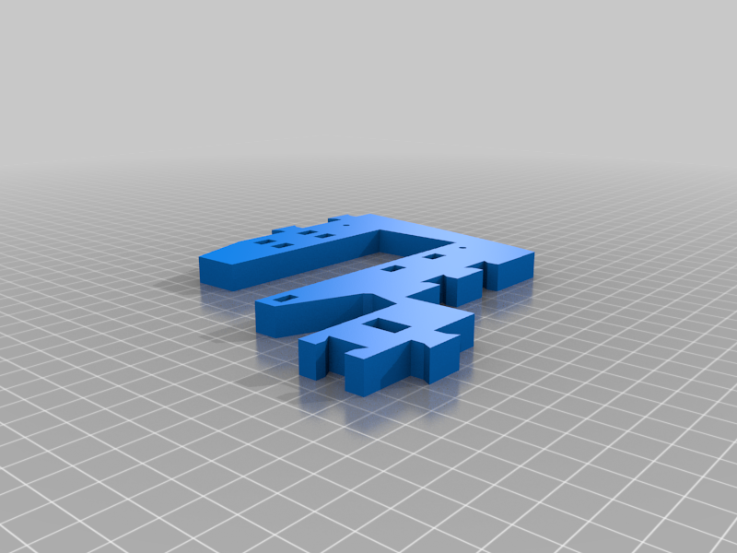
3D_Printing_Files/Robot/Inmoov Chest - 2175499/images/3088fcb493d6a2ad61c758510ab16376.png
