KevinQuigs/ECE1896-Force-Feedback-Telepresence-Robot/3D_Printing_Files/Robot/Inmoov Chest - 2175499/images/4254d239db04e475a1a5e8bdfbbec089.png

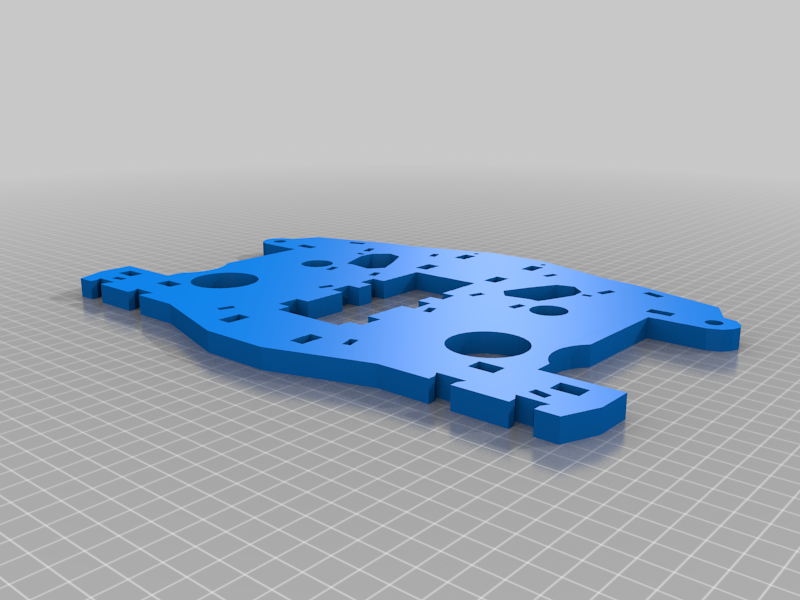
3D_Printing_Files/Robot/Inmoov Chest - 2175499/images/4254d239db04e475a1a5e8bdfbbec089.png
