KevinQuigs/ECE1896-Force-Feedback-Telepresence-Robot/3D_Printing_Files/Robot/Inmoov Chest - 2175499/images/6370bb0e9d32a54d528ca591780fbc7b.png

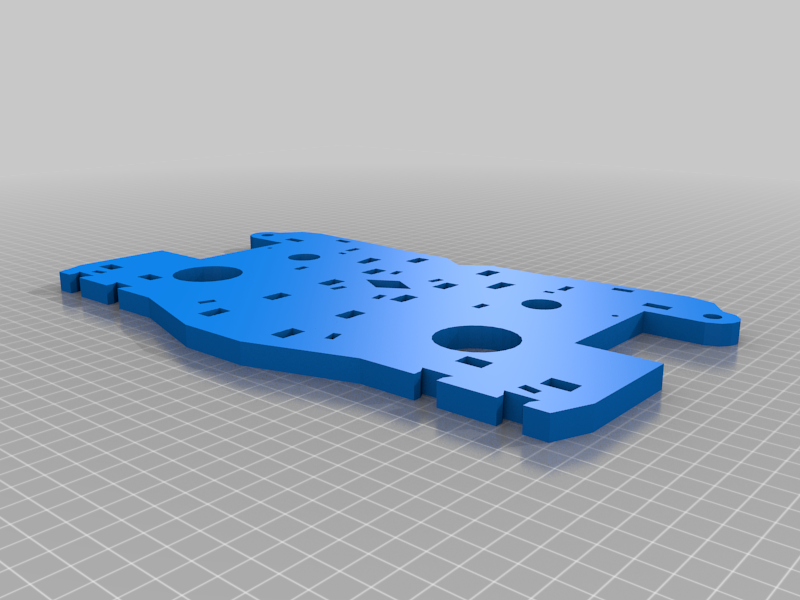
3D_Printing_Files/Robot/Inmoov Chest - 2175499/images/6370bb0e9d32a54d528ca591780fbc7b.png
