KevinQuigs/ECE1896-Force-Feedback-Telepresence-Robot/3D_Printing_Files/Robot/Inmoov Chest - 2175499/images/1158738ace5efbf3b3b23fea3fe77a4e.png

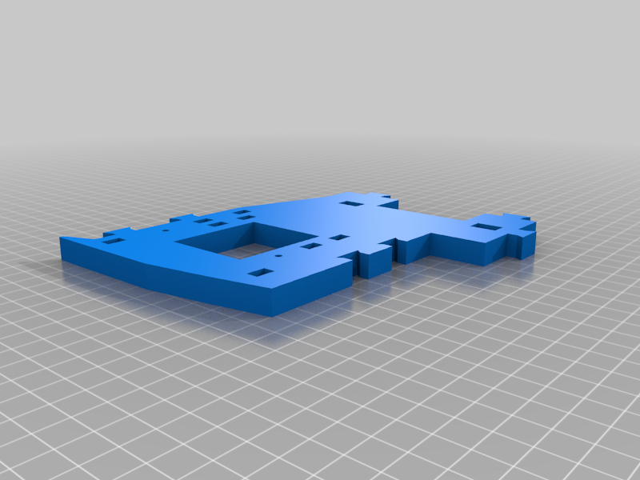
3D_Printing_Files/Robot/Inmoov Chest - 2175499/images/1158738ace5efbf3b3b23fea3fe77a4e.png
