KevinQuigs/ECE1896-Force-Feedback-Telepresence-Robot/3D_Printing_Files/Robot/Inmoov Chest - 2175499/images/a50f041775ac87b49871989c897ef9ec.png

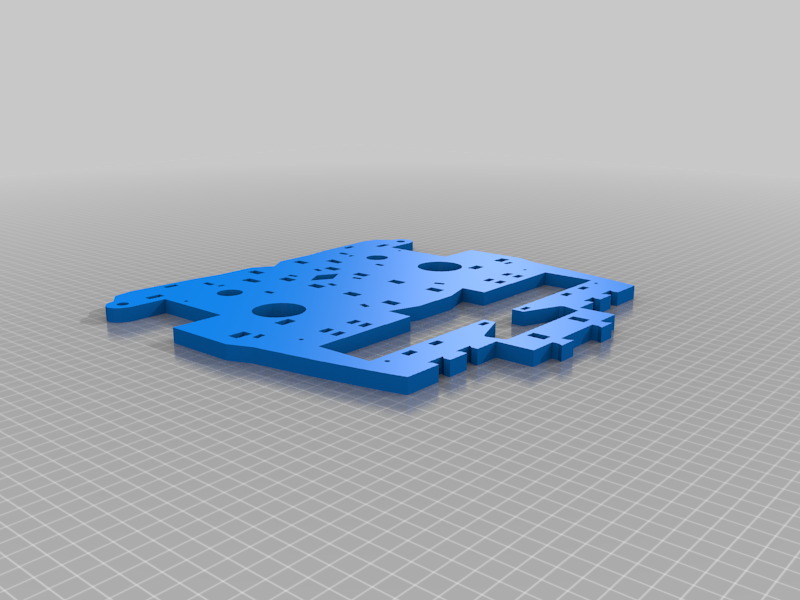
3D_Printing_Files/Robot/Inmoov Chest - 2175499/images/a50f041775ac87b49871989c897ef9ec.png
