KevinQuigs/ECE1896-Force-Feedback-Telepresence-Robot/3D_Printing_Files/Robot/Inmoov Chest - 2175499/images/c59f1257a8f105b107a7d3e83ffe0dc6.png

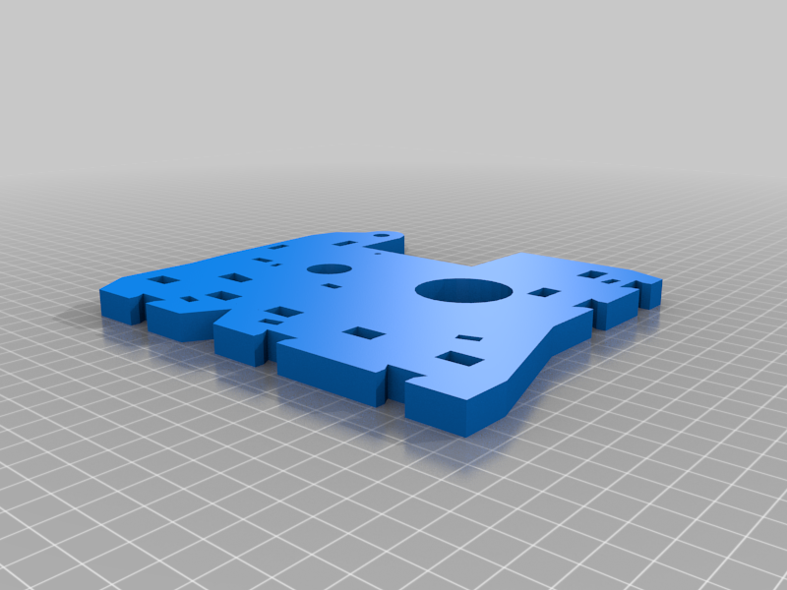
3D_Printing_Files/Robot/Inmoov Chest - 2175499/images/c59f1257a8f105b107a7d3e83ffe0dc6.png
