KevinQuigs/ECE1896-Force-Feedback-Telepresence-Robot/3D_Printing_Files/Robot/Inmoov Chest - 2175499/images/Chest_Orignal.jpg

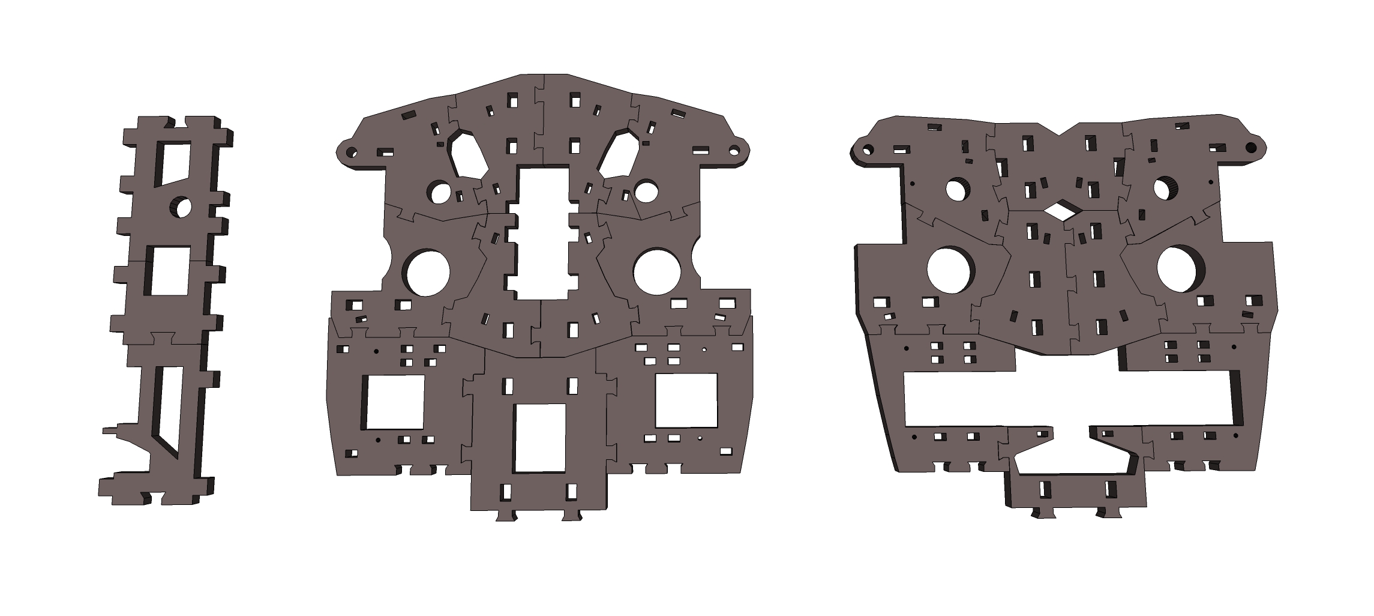
3D_Printing_Files/Robot/Inmoov Chest - 2175499/images/Chest_Orignal.jpg
