KevinQuigs/ECE1896-Force-Feedback-Telepresence-Robot/3D_Printing_Files/Robot/Inmoov Chest - 2175499/images/def60a5dba5c54410128e2acab6650db.png

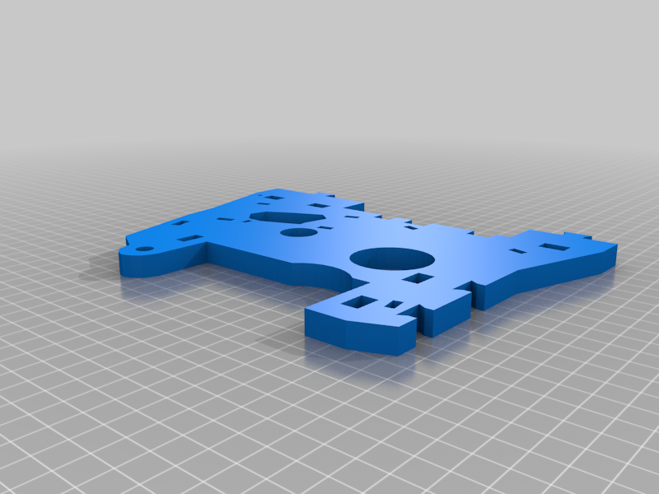
3D_Printing_Files/Robot/Inmoov Chest - 2175499/images/def60a5dba5c54410128e2acab6650db.png
