KevinQuigs/ECE1896-Force-Feedback-Telepresence-Robot/3D_Printing_Files/Robot/Inmoov Chest - 2175499/images/f7592fcdc1255b70c876d41e8632403f.png

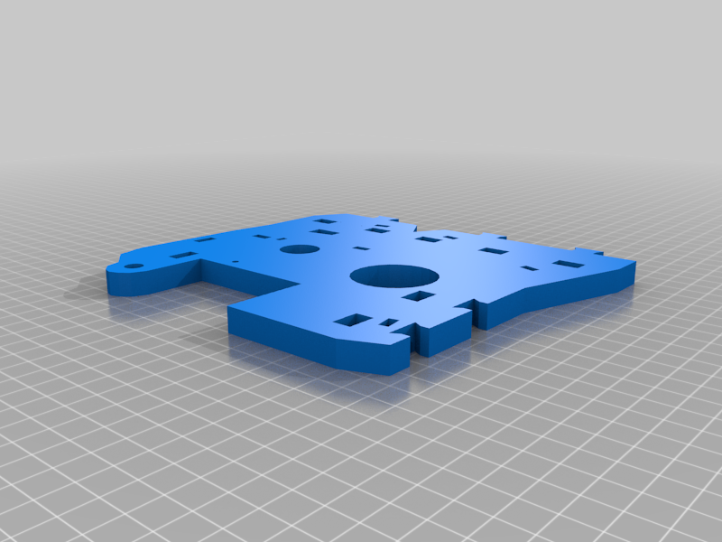
3D_Printing_Files/Robot/Inmoov Chest - 2175499/images/f7592fcdc1255b70c876d41e8632403f.png
