KevinQuigs/ECE1896-Force-Feedback-Telepresence-Robot/Code/Robotic_Neck/C++/_main.ino

ICommunication* comm;
int loops = 0;
void setup() {
  #if COMMUNICATION == COMM_SERIAL
    comm = new SerialCommunication();
  #elif COMMUNICATION == COMM_BTSERIAL
    comm = new BTSerialCommunication();
  #endif  
  comm->start();

  setupInputs();

  #if USING_FORCE_FEEDBACK
    setupServoHaptics();  
  #endif
  
}

void loop() {
  if (comm->isOpen()){
    
    comm->output(encode(fingerPos, getJoyX(), getJoyY(), joyButton, triggerButton, aButton, bButton, grabButton, pinchButton, calibButton, menuButton));
  }
}
