KevinQuigs/ECE1896-Force-Feedback-Telepresence-Robot/Code/FF-Glove/FF-Glove-Final/haptics.ino

#if USING_FORCE_FEEDBACK

#if defined(ESP32)
  #include "ESP32Servo.h"
#else
  #include "Servo.h"
#endif

Servo pinkyServo;
Servo ringServo;
Servo middleServo;
Servo indexServo;
Servo thumbServo;

void setupServoHaptics(){
  pinkyServo.attach(PIN_PINKY_MOTOR);
  ringServo.attach(PIN_RING_MOTOR);
  middleServo.attach(PIN_MIDDLE_MOTOR);
  indexServo.attach(PIN_INDEX_MOTOR);
  thumbServo.attach(PIN_THUMB_MOTOR);
}

//static scaling, maps to entire range of servo
void scaleLimits(int* hapticLimits, float* scaledLimits){
  for (int i = 0; i < 5; i++){
    scaledLimits[i] = 180.0f - hapticLimits[i] / 1000.0f * 180.0f;
  }
}

//dynamic scaling, maps to the limits calibrated from your finger
void dynScaleLimits(int* hapticLimits, float* scaledLimits){
  //will be refactored to take min and max as an argument

  /* this implementation of dynamic scaling relies on the assumption 
   * that the servo reaches 2/3 of the potentiometer's range, 
   * and that 0 degrees is geared to the start of the potentiometer.
   * Different hardware types may need to handle dynamic scaling differently.
   */
  for (int i = 0; i < sizeof(hapticLimits); i++){
    scaledLimits[i] = hapticLimits[i] / 1000.0f * 180.0f;
  }
}

void writeServoHaptics(int* hapticLimits){
  float scaledLimits[5];
  scaleLimits(hapticLimits, scaledLimits);
  if(hapticLimits[0] >= 0) thumbServo.write(scaledLimits[0]);
  else thumbServo.write(0);
  if(hapticLimits[1] >= 0) indexServo.write(scaledLimits[1]);
  else indexServo.write(0);
  if(hapticLimits[2] >= 0) middleServo.write(scaledLimits[2]);
  else middleServo.write(0);
  if(hapticLimits[3] >= 0) ringServo.write(scaledLimits[3]);
  else ringServo.write(0);
  if(hapticLimits[4] >= 0) pinkyServo.write(scaledLimits[4]);
  else pinkyServo.write(0);
}

#endif
