KevinQuigs/ECE1896-Force-Feedback-Telepresence-Robot/Code/FF-Glove/FF-Glove-Final/ICommunication.ino

//Interface for communication

class ICommunication {

  public:
    virtual bool isOpen() = 0;

    virtual void start() = 0;

    virtual void output(char* data) = 0;

    virtual bool readData(char* input) = 0;
};
