KevinQuigs/ECE1896-Force-Feedback-Telepresence-Robot/Code/FF-Glove/FF-Glove-Final/SerialCommunication.ino

class SerialCommunication : public ICommunication {
  private:
    bool m_isOpen;

  public:
    SerialCommunication() {
      m_isOpen = false;
    }

    bool isOpen(){
      return m_isOpen;
    }

    void start(){
      //Serial.setTimeout(1000000);
      Serial.begin(115200);
      m_isOpen = true;
    }

    void output(char* data){
      Serial.print(String(data).encode());
      Serial.flush();
    }

    bool readData(char* input){
      byte size = Serial.readBytesUntil('\n', input, 100);
      input[size] = NULL;
      return input != NULL && strlen(input) > 0;
    }
};
