KevinQuigs/ECE1896-Force-Feedback-Telepresence-Robot/Code/FF-Glove/FF-Glove-Final/input.ino

// Requires RunningMedian library by Rob Tillaart
#if ENABLE_MEDIAN_FILTER
  #include <RunningMedian.h>
  RunningMedian rmSamples[5] = {
      RunningMedian(MEDIAN_SAMPLES),
      RunningMedian(MEDIAN_SAMPLES),
      RunningMedian(MEDIAN_SAMPLES),
      RunningMedian(MEDIAN_SAMPLES),
      RunningMedian(MEDIAN_SAMPLES)
  };
#endif

int maxFingers[5] = {0,0,0,0,0};
int minFingers[5] = {ANALOG_MAX, ANALOG_MAX, ANALOG_MAX, ANALOG_MAX, ANALOG_MAX};

void setupInputs(){
  #if USING_CALIB_PIN
  pinMode(PIN_CALIB, INPUT_PULLUP);
  #endif
}

int* getFingerPositions(bool calibrating, bool reset){
  int rawFingers[5] = {analogRead(PIN_THUMB), analogRead(PIN_INDEX), analogRead(PIN_MIDDLE), analogRead(PIN_RING), analogRead(PIN_PINKY)};

  //flip pot values if needed
  #if FLIP_POTS
  for (int i = 0; i <5; i++){
    rawFingers[i] = ANALOG_MAX - rawFingers[i];
  }
  #endif

  #if ENABLE_MEDIAN_FILTER
  for (int i = 0; i < 5; i++){
    rmSamples[i].add( rawFingers[i] );
    rawFingers[i] = rmSamples[i].getMedian();
  }
  #endif

  //reset max and mins as needed
  if (reset){
    for (int i = 0; i <5; i++){
      maxFingers[i] = 0;
      minFingers[i] = ANALOG_MAX;
    }
  }
  
  //if during the calibration sequence, make sure to update max and mins
  if (calibrating){
    for (int i = 0; i <5; i++){
      if (rawFingers[i] > maxFingers[i])
        #if CLAMP_FLEXION
          maxFingers[i] = ( rawFingers[i] <= CLAMP_MAX )? rawFingers[i] : CLAMP_MAX;
        #else
          maxFingers[i] = rawFingers[i];
        #endif
      if (rawFingers[i] < minFingers[i])
        #if CLAMP_FLEXION
          minFingers[i] = ( rawFingers[i] >= CLAMP_MIN )? rawFingers[i] : CLAMP_MIN;
        #else
          minFingers[i] = rawFingers[i];
        #endif
    }
  }

  static int calibrated[5] = {511,511,511,511,511};
  
  for (int i = 0; i<5; i++){
    if (minFingers[i] != maxFingers[i]){
      calibrated[i] = map( rawFingers[i], minFingers[i], maxFingers[i], 0, ANALOG_MAX );
      #if CLAMP_ANALOG_MAP
        if (calibrated[i] < 0)
          calibrated[i] = 0;
        if (calibrated[i] > ANALOG_MAX)
          calibrated[i] = ANALOG_MAX;
      #endif
    }
    else {
      calibrated[i] = ANALOG_MAX / 2;
    }
  }
  return calibrated;
  
}


bool getButton(byte pin){
  return digitalRead(pin) != HIGH;
}
